openkeyboard-org/OpenDongle/firmware/common/src/rf_task.c

/*
 * UNIFIED RF task body (P6, 2026-06-11 colocation → 2026-07-07 unification):
 * the single 2.4G RF receiver run by ALL THREE chips (CH592, CH582, CH570).
 * Originated as the CH59x (CH592F product) body; the CH570 legacy body
 * (rf_task_ch570.c) converged onto it and was deleted in P6. Chip differences
 * survive only behind the hal seams (hal_timing / hal_rf / hal_dispatch) and
 * the RF_TASK_EXECUTOR_TMOS family switch. Includes resolve per-chip via the
 * building tree's -I src / -I common/include (rf_task.h, CONFIG.h etc.).
 *
 * OpenKeyboard.org OpenDongle
 * Copyright 2026 Eric Molitor (EMulator)
 * SPDX-License-Identifier: Apache-2.0
 * 2.4G RF Receiver Task
 *
 * Reverse-engineered protocol parameters from stock firmware.
 * See PROTOCOL.md for full specification.
 */

#include "dongle_target.h"      /* RF_TASK_EXECUTOR_TMOS + tick constants */
#include "dongle_platform.h"
#if RF_TASK_EXECUTOR_TMOS
#include "CONFIG.h"   /* TMOS: the CH59x-family executor (registration + timers) */
#include "HAL.h"
#endif
#include "dongle_chip.h"   /* per-tree SDK common header; supplies the __risc_v_*
                            * critical-section shim on CH582 (the ch583 SDK's
                            * core_riscv.h predates it -- see ch582 dongle_chip.h) */
#include "rf_task.h"
#include "bond.h"

/* CH570 pair-ACK pre-TX gap (V1, bench-derived 2026-07-10). The real Bridge75
 * needs 1..8 ms between its PAIR_BCAST and our 15-byte pair-ACK; answering
 * immediately misses its receive window and the link flaps forever. The
 * shipping build supplied this ACCIDENTALLY, as the ~6.3 ms busy-wait of
 * PRINT("PAIR_BCAST ..."). Schedule it instead: a delayed post runs the
 * existing RF_EVT_TX_PAIR_15 handler from the pump, so nothing blocks the
 * radio IRQ.
 *
 * Expressed in TMOS units (625 us) like every other delay in this file --
 * hal_event_post_delayed() takes Tsys ticks and CH592 converts back with
 * hal_tmos_units_from_tsys(), so a raw microsecond value would silently
 * quantize there (2000 us -> 3 units -> 1875 us). Stating the unit count makes
 * the quantization explicit and keeps the constant portable if CH59x ever
 * needs the same gap.
 *
 * Sweep: 0 -> 0/3, 500 us -> 2/3, 1000/2000/6337 us -> 3/3, 12 ms -> 1/3,
 * 20 ms -> 0/3. Per-value reconnect quality (bench): 1875 us -> 6/6 but
 * 0.22 s / up to 12 flips; 2500 us -> 8/8, 0.11 s, 0-1 flips (chosen: 4 units).
 * Value set by each target's dongle_target.h. */
#ifndef RF_CH570_PAIR_ACK_PRE_TX_TMOS
#error "RF_CH570_PAIR_ACK_PRE_TX_TMOS must be defined by the target header"
#endif

/* Confirm-before-persist gate (Issue #23): defer the durable bond write until a
 * connected RX confirms the peer accepted the session. Named as its own feature
 * so both executors can share the state machine (the durable-arm site and the
 * CX4 write stay per-executor). Every target header must set it explicitly. */
#ifndef RF_CONFIRM_BEFORE_PERSIST
#error "RF_CONFIRM_BEFORE_PERSIST must be defined by the target header"
#endif

#include "usb_device.h"
#include "hal_timing.h"        /* RF deadline-scheduler seam */
#include "hal_timing_ch592.h"  /* CH592 task-dispatch shim (CONNECTED_POLL slot) */
#include "hal_dispatch.h"      /* deferred-event seam (chip header aliases above) */
#if !RF_TASK_EXECUTOR_TMOS
/* CX1 (codex): CONNECTED-state RF re-arms are timing-critical (the keyboard
 * replies inside the ~875 us window) and the CH570 pump's worst-case latency
 * under EP6 IAP flash traffic is milliseconds — so on this executor the
 * radio-IRQ sink arms them SYNCHRONOUSLY (its validated legacy shape). On
 * TMOS they stay posted events (the validated CH59x shape — CX2). */
static void rf_arm_post_poll_rx(void);
static void rf_rearm_rx(void);
#define RF_CONNECTED_POST_POLL_RX_ARM() rf_arm_post_poll_rx()
#define RF_CONNECTED_RX_REARM()         rf_rearm_rx()
/* CH570 hardware poll grid (ch570/Makefile knob; 0 on other !TMOS ports).
 * When set, the connected-poll cadence is a hardware auto-reload grid
 * anchored at the pair/re-key TX and PROMOTED by ownership transfer
 * (hal_timer_promote_periodic -> st_periodic_transfer, zero hardware
 * writes) instead of re-armed at the promote instant — the CH592 TMR0
 * phase-lock mirror. See analysis/ch570-hw-poll-grid/baseline.md for the
 * +3380 ppm software-grid drift this replaces. */
void hal_timer_promote_periodic(uint8_t from_slot, uint8_t to_slot,
                                uint32_t fallback_period,
                                hal_timer_cb_t cb);  /* hal_timing_ch570.c */
uint8_t hal_timer_grid_nudge(uint32_t ticks);        /* hal_timing_ch570.c */
/* Phase acquisition (Codex option C, 2026-07-08). A crystal-flat grid that
 * starts outside the sleeping keyboard's narrow RX window misses it
 * IDENTICALLY forever (real-Bridge75 finding: promote+bond OK, rx=0 for
 * every poll at two different anchors). The v0.96 software timer acquired
 * by accident: its +3380 ppm drift (~+3 us/poll) swept the phase across the
 * slot until a poll landed and the keyboard's ±31 us/packet servo locked.
 * Deliberate version: start the first period at the promote anchor plus a
 * fixed offset (v0.96's effective mod-slot phase ≈ the ~9.7 ms print delay
 * ≈ +75 us; replace with the measured CH592 value when its probe returns),
 * then, while CONNECTED with zero poll responses, stretch the grid +8 us
 * per poll (Codex band 4-8 us — bigger steps can hop a narrow window) until
 * the first reply, then hold flat.
 * N10 SCOPE (CODEREVIEW, accepted residual): this sweep is LOCAL to one
 * uninterrupted grid — a ~26-poll session covers ~0..267 us, and the step
 * counter does NOT carry physical phase into the next re-anchored session, so
 * full-slot cross-session tiling is NOT achieved. The stock Bridge75 locks in
 * practice (production-validated); a true cumulative-phase primitive is
 * deferred pending a phase-controllable failing control. See rf_ch570_acq_arm
 * and analysis/codex-review-campaign-2026-07-17/change12-N10-sweep-spike.md. */
#define RF_CH570_GRID_PHASE_OFFSET_TICKS 7500u   /* 75 us @100 MHz */
#define RF_CH570_ACQ_STEP_TICKS 800u             /* 8 us per poll */
#define RF_CH570_ACQ_MAX_NUDGES 150u   /* 150*8us=1.2ms; > one full slot only
                                        * at the stock 28-tick interval (875us
                                        * slot) — a larger provisioned interval
                                        * (up to 300 -> 9.375ms slot) is NOT
                                        * covered by this fixed cap (N10) */
static void rf_ch570_acq_arm(uint8_t seed);  /* flash helper below */
static volatile uint32_t rf_ch570_acq_base; /* RX tally at promote:
                                         * ANY connected RX freezes the
                                         * sweep (Codex: the first reply may
                                         * be a LEN-10 HID report, not a
                                         * LEN-1 poll response)             */
static volatile uint32_t rf_ch570_acq_nudges;
/* No TMOS on this executor: map the TMOS mem helpers the body uses onto the
 * builtins. NOTE tmos_memcmp is TRUE-when-EQUAL (BLE-lib convention). */
#define tmos_memcpy(dst, src, n) __builtin_memcpy((void *)(dst), (const void *)(src), (n))
#define tmos_memset(dst, v, n)   __builtin_memset((void *)(dst), (v), (n))
#define tmos_memcmp(a, b, n)     (__builtin_memcmp((const void *)(a), (const void *)(b), (n)) == 0)
/* The sink's internal sta vocabulary — numerically the CH59x BLE-lib codes
 * (CH59xBLE_LIB.h) so telemetry stays comparable across chips. */
#define TX_MODE_TX_FINISH 0x01
#define RX_MODE_RX_DATA   0x03
#define TX_MODE_TX_FAIL   0x11
#else
#define RF_CONNECTED_POST_POLL_RX_ARM() hal_event_post(RF_EVT_POST_POLL_RX)
#define RF_CONNECTED_RX_REARM()         hal_event_post(RF_EVT_RX_RESTART)
#endif
#include "hal_rf.h"             /* RF PHY seam */
#include "rf_protocol.h"        /* shared on-air protocol facts (phase A) */
#include "rf_supervision.h"     /* stock-style supervision timing helpers */

#if !RF_TASK_EXECUTOR_TMOS
/* The acquisition sweep stops as soon as any connected packet is received. */
static volatile uint32_t rf_ch570_connected_rx_count;
#endif
/* RF arm status is recorded in IRQ and task context; task-context guard sites
 * consume it and re-arm when needed. */
volatile uint8_t  rf_last_arm_status;
#if !RF_TASK_EXECUTOR_TMOS
/* Cold-boot SRAM entropy: main() hashes the pristine power-on state of the free
 * RAM gap into this word before normal stack use, and the session-AA RNG mixes
 * it into its seed so each cold boot (i.e. each replug,
 * i.e. each fresh pair in practice) gets a distinct, unpredictable AA rather
 * than the UID-deterministic value. Costs one word — the hashed RAM is the
 * normal stack/heap, not reserved. See ch570_capture_boot_entropy() in main.c. */
volatile uint32_t rf_ch570_boot_entropy;
#endif

/* Supervision/re-acquire runs the production CH592 stock shape — the
 * bench-validated v0.93+ product behavior on every build path (including the
 * CH582 port and direct sub-targets). The legacy OpenDongle-style recovery
 * flavor and its CH592_STOCK_EV10_EXPERIMENT A/B flag were retired in the
 * unify-rf-task P1a collapse (flag had defaulted to 1 since v0.94). */

#define CH592_STOCK_EV10_LAPSE_MARGIN_TICKS 128u
#define CH592_STOCK_EV10_RECOVERY_CONFIRM_WINDOWS 1u
#define RF_RTC_BACKSTEP_TOLERANCE_TICKS 1024u

/* ---------- RF PHY parameters (from firmware RE) ---------- */

/* The product boots directly into the raw 2.4 GHz listener on its configured
 * access address and channel. Pair completion persists the bond to DataFlash
 * so the dongle reconnects after a reboot without reprovisioning. */

/* Promote after this numbered session-AA burst has completed locally.
 * Stock promotes from state 1 on TX_MODE_TX_FINISH; it does not wait for
 * a six-packet recovery burst. The current 08FD/CEBD reconnect bench
 * shows the keyboard reporting CONNECTED after burst #1, so default to
 * the stock-shaped early promote and keep the old "after all bursts"
 * behavior. */
#define RF_BURST_PROMOTE_AFTER_SESSION_BURST 1

#if RF_BURST_PROMOTE_AFTER_SESSION_BURST < 1 || RF_BURST_PROMOTE_AFTER_SESSION_BURST > 6
#error "RF_BURST_PROMOTE_AFTER_SESSION_BURST must be in 1..6"
#endif

/* Tick gap between burst TXes. 1 TMOS tick = 625 µs on CH58x.
 *
 * The keyboard's first-pair branch in FUN_ram_20001192 does two DataFlash
 * persists (FUN_ram_00009a40 writes MAC at flash 0x6000, FUN_ram_00009aa4
 * writes AA at flash 0x4000), each = page-erase (~25ms) + page-write
 * (~5ms). Total RF-callback blocking time: ~50-100 ms before the radio
 * reconfig completes and the library re-arms RX on the new session AA.
 *
 * An immediate-fire burst (tmos_set_event, ~0 ms gap) lands entirely
 * inside that blocked window — verified live: 6 TXes fired in 101 ms,
 * keyboard state stayed 0x35. Pacing each burst TX 80 ticks (~50 ms)
 * apart puts burst#2 at +50ms, burst#3 at +100ms, etc. — burst#3..5 are
 * past the DataFlash blocking window and should land on a re-armed
 * keyboard RX.
 *
 */
#define RF_PAIR_ACK_BURST_GAP 80

/* Pair-completion defaults. Keep these before static initializers that
 * reference them.
 *
 * RF_SESSION_ACCESS_ADDR: session AA we'll advertise in the pair-completion.
 * Must match one of the dongle's generator patterns. 0x6A7DAEE6 was dumped
 * live from the stock dongle's SRAM so we know it passes validation.
 *
 * RF_DONGLE_MAC_*: MAC we'll advertise as the "dongle" in the 15-byte
 * pair-completion frame. Two valid choices depending on the test target:
 *   (a) Bench test against a fresh CH592F dev board running stock keyboard
 *       fw (no stored peer): use this chip's own factory BLE MAC so the
 *       bond is durable across reboots. Default below.
 *   (b) Field test against a real Bridge75 keyboard already bonded to its
 *       stock dongle: use the stock dongle's MAC 0xBA 0x47 0x8B 0x72 0xAB
 *       0x3C (read live from its SRAM at 0x20003849..0x2000384E) so the
 *       keyboard matches us on the known-peer branch without touching its
 *       pairing memory.
 * The advertised dongle MAC is held at runtime in rf_bond_dongle_mac,
 * defaulting to RF_DONGLE_MAC_* and overridden from the DataFlash bond
 * record. */
#define RF_SESSION_ACCESS_ADDR   0x6A7DAEE6u
#define RF_DONGLE_MAC_0 0xD1
#define RF_DONGLE_MAC_1 0x4C
#define RF_DONGLE_MAC_2 0x85
#define RF_DONGLE_MAC_3 0x26
#define RF_DONGLE_MAC_4 0x3B
#define RF_DONGLE_MAC_5 0x38

/* 15-byte pair-ACK payload. The session access address and dongle MAC must
 * match the advertised session identity for reconnect tests; otherwise the
 * keyboard can receive a completion packet but enter connected mode on the
 * wrong AA / peer identity. */
/* RF_PAIR_TIMEOUT — advertised conn_timeout in our 15-byte pair-ACK.
 * Default 600 matches what the keyboard's pair broadcast advertises. */
#define RF_PAIR_TIMEOUT RF_PROTO_DEFAULT_TIMEOUT
#define RF_PAIR_ACK15_ACCESS_ADDR RF_SESSION_ACCESS_ADDR

static uint8_t rf_pair_ack15[15] = {
    /* session access addr (MSB-first u32) */
    (uint8_t)((RF_PAIR_ACK15_ACCESS_ADDR >> 24) & 0xFF),
    (uint8_t)((RF_PAIR_ACK15_ACCESS_ADDR >> 16) & 0xFF),
    (uint8_t)((RF_PAIR_ACK15_ACCESS_ADDR >>  8) & 0xFF),
    (uint8_t)( RF_PAIR_ACK15_ACCESS_ADDR        & 0xFF),
    /* type tag (also seeds the data-hop index on both ends via % 5) */
    RF_PROTO_PAIR_ACK_TYPE,
    /* conn_interval (u16 LE) = 0x001C = 28. MUST match the keyboard's
     * advertised conn_interval in PAIR_BCAST. The keyboard hops data
     * channels every conn_interval protocol ticks of 1/32000 s
     * (= 875 µs at 28 — the "32K" clock is the calibrated 32000 Hz
     * LSI, not 32768 Hz); our TMR0 POLL cadence derives from this same
     * value via rf_tmr0_steady_count(). Advertising 0x001E = 30 (the
     * previous value) caused a ~10% rate mismatch: fw-ch592f polls at
     * 937 µs while the keyboard hops at 875 µs, so polls land outside the
     * keyboard's RX window after a few hops and the link drops at
     * ~3 s. Found 2026-05-20 via keyboard SRAM dump (rx_count=0
     * post-CONNECTED). See
     * analysis/fw-ch592f-vs-stock-audit-2026-05-20.md G3. */
    (uint8_t)(RF_PROTO_DEFAULT_INTERVAL & 0xFF),
    (uint8_t)((RF_PROTO_DEFAULT_INTERVAL >> 8) & 0xFF),
    /* conn_timeout (u16 LE) — RF_PAIR_TIMEOUT bytes LE */
    (uint8_t)(RF_PAIR_TIMEOUT & 0xFF),
    (uint8_t)((RF_PAIR_TIMEOUT >> 8) & 0xFF),
    /* our (dongle) MAC */
    RF_DONGLE_MAC_0, RF_DONGLE_MAC_1, RF_DONGLE_MAC_2,
    RF_DONGLE_MAC_3, RF_DONGLE_MAC_4, RF_DONGLE_MAC_5,
};

/* Burst state machine — accessed from both IRQ (TX_FINISH callback) and
 * task context (RF_EVT_TX_PAIR_15B handler). volatile for IRQ safety. */
volatile uint8_t rf_inject_burst_active = 0;
volatile uint8_t rf_inject_burst_idx = 0;  /* 0..5, 0 = first TX in flight */

/* Channel set for the burst. The keyboard's first-pair radio reconfig
 * (FUN_ram_000072e6 in firmwareB.bin) does only RF_Shut + RF_Config —
 * it sets the session AA but does NOT change channel. So immediately
 * after first-pair the keyboard is listening on session AA on whichever
 * pair channel it last broadcast on (∈ {8, 17, 26}). Hitting the data
 * LUT {4, 13, 20, 28, 33} therefore misses the keyboard entirely in
 * state==1. Burst on the pair LUT instead.
 *
 * Two rounds of the shared pair LUT (rf_pair_channels, declared below from
 * RF_PROTO_PAIR_CHANNELS_INIT) give 6 chances spaced over the burst window —
 * biases for the keyboard's listen channel being one of those three. The
 * burst indexes the LUT modulo its size (rf_burst_channel(idx)) so a
 * pair-channel change in rf_protocol.h propagates here automatically. */
#define RF_BURST_TX_COUNT (2u * RF_PROTO_PAIR_CHANNEL_COUNT)

volatile uint8_t rf_supervision_ev10_active = 0;

/* LED-relay queue counter — increments each time rf_queue_led_relay() queues a
 * host LED byte for the poll path. SWD oracle to confirm the relay was queued
 * (the on-air TX is then confirmed by the keyboard's 5A status). */

/* 1760u diag: count faithful-EV10 attempts that completed (caught
 * the LEN-10, sent the LEN-15 re-key, returned to CONNECTED) vs aborted (no
 * LEN-10 in the budget). */

/* Hop-clock timestamp (rf_hop_read(): HSE-derived protocol ticks) captured at
 * the EV10 LEN-15 re-key RF_Tx. Used by RF_EV10_GRID_ALIGNED_POLL to phase
 * the first resumed data poll to rekey_TX + 1 interval (stock's measured
 * convention), independent of the post-TX reconfigure latency. */
volatile uint32_t rf_ev10_rekey_tx_hop;

/* Stock-shaped queued app payload. Per disasm of stock firmware.bin,
 * event 0x80 (LED relay) doesn't transmit directly — it queues
 * [0xA1, LED_byte] and the normal event 0x02 (poll) helper prepends
 * the control byte and sends as [ctrl][0xA1][LED_byte] in the next
 * poll slot. Same TMR0 cadence, same hop schedule — the keyboard's
 * CONNECTED-state RX only listens in those slots, so out-of-band
 * direct LED TX lands in dead air.
 *
 * rf_app_tx_pending nonzero ⇒ rf_send_poll consumes the queue
 * (sends 3-byte [ctrl,buf[0],buf[1]] instead of 1-byte [ctrl]) while
 * decrementing the count. Stock parity: a single LEN=3 relay per host LED
 * change + one at connect/reconnect -- no burst, no periodic heartbeat. */
volatile uint8_t  rf_app_tx_pending;
volatile uint8_t  rf_app_tx_buf[2];

/* Queue the host->keyboard LED relay payload [0xA1][led] so the next connected
 * poll sends it as [ctrl][0xA1][led] (rf_send_poll consumes rf_app_tx_pending).
 * Replaces the stock-shaped delayed RF_EVT_POST_PROMOTE_LED3 event, which the
 * supervision/EV10 rebind paths cancelled before it could fire (the relay never
 * transmitted). The queue buffer is NOT cancelled by those rebind stop sites, so
 * it survives to the next valid poll. Caller contexts are NOT both cooperative:
 * RF_SetLEDState runs in TMOS task context, but the burst-promote re-sync runs
 * inside rf_phy_event_sink -- an IRQ-tail deferred callback that CAN preempt
 * task context (see the P2.4 note at the sink). No IRQ critical section is
 * needed anyway because every shared item (rf_led_state, rf_app_tx_buf bytes,
 * rf_app_tx_pending) is a single volatile byte (atomic on RV32), preemption is
 * strictly one-way (sink over task, never the reverse), and the foreground
 * latches rf_led_state BEFORE any queue access -- so every interleaving
 * converges to the queue holding the current LED byte with pending=1. */
static __attribute__((noinline)) void rf_queue_led_relay(uint8_t led)
{
    rf_app_tx_buf[0]  = RF_PROTO_HID_TAG;
    rf_app_tx_buf[1]  = (uint8_t)(led & 0x07u);
    rf_app_tx_pending = 1u;          /* stock parity: single LEN=3 relay, fire-and-forget */
}

/* Stock dispatcher event 0x04 calls RF_Rx(gp-0x604, 10, 0xff, 0xff):
 * the same control/poll buffer used by empty-poll RF_Tx, but with RX
 * length 10. The shared poll/RX buffer itself is the normal rf_poll_buf below. */

/* Product reconnect default. */
#define RF_DEFAULT_ACCESS_ADDR  0xAC1649CEu


/* CRC initial value */
/* CRC init + LLE mode moved to hal_rf_ch592.c (P2.4) -- the PHY seam owns
 * the rfConfig_t construction. */

/* LLE mode: 2M PHY | basic mode | whitening ON | channel index | RSSI byte */
/* Stock dongle's rfConfig.LLEMode = 0x10 (BASIC + WHITENING_ON +
 * PHY_2M) per the OQ7 SRAM dump. Keyboard uses 2M PHY. Bench-proven
 * 2026-05-17: with PFIC_EnableIRQ(BLEB|BLEL) + RF_Rx(NULL,0,...) +
 * LLEMode=0, fw-ch592f receives 241 RX_DATA callbacks/10s on BLE
 * ADV ch37 (1M PHY). Restoring LLEMode=0x10 for 2M PHY compatibility
 * with the keyboard's proprietary 2.4G protocol. */

/* Minimum RSSI for pair acceptance (dBm). Gates the fresh-pair path (no
 * valid bond) AND a boot-window accept of a DIFFERENT keyboard; the
 * known-peer reconnect path has no RSSI gate (a bonded keyboard must
 * reconnect at range).
 *
 * This floor has now been raised twice for the same reason, which is the
 * point worth carrying forward: -55 rejected most real captures, and -75
 * rejected the product's primary scenario. Bisected with diagnostic builds
 * on stock v0.96.15 with a bonded link: -128 accepted, -90 accepted, -82
 * accepted, -75 REJECTED. So the keyboard's pair broadcast arrives at
 * -81..-76 dBm with both boards on one bench - i.e. -75 had NEGATIVE margin
 * at legitimate pairing distance, and a dongle behind a PC case or across a
 * desk sits in that band or below.
 *
 * -90 keeps what the gate is actually for. Its job is stopping an
 * unprovisioned dongle auto-pairing with a distant keyboard in a dense
 * environment; at 2.4 GHz a cross-room signal (several metres plus a wall)
 * generally lands below -90 while same-room stays above it. That preserves
 * the "not the neighbour's office" property with ~10 dB over what we
 * measured, instead of defending a threshold the bench already fails.
 *
 * Treat this as a heuristic sanity floor, not a security boundary. CH59x
 * RSSI is coarse and uncalibrated chip to chip, so the same number means
 * different real distances on different units, and the gate is reported
 * inert on the CH570 SKU (its RSSI byte reads constant) - so the product
 * line already tolerates a no-gate configuration.
 *
 * If mispairing in dense environments ever becomes a real complaint, the
 * fix is NOT a tighter floor: it is strongest-candidate selection - collect
 * broadcasters briefly during pairing and take the highest RSSI, keeping
 * this only as a sanity floor. An absolute threshold encodes antenna and
 * geometry assumptions; relative selection targets the actual failure mode.
 *
 * Overridable for bench profiles without editing source (this file is shared,
 * so substitute the chip you are building):
 *   make -C firmware ch570 PAIR_MIN_RSSI=-95
 *   make -C firmware ch592 PAIR_MIN_RSSI=-95
 * The live value is readable over IAP (status byte
 * DONGLE_STATUS_OFF_LAST_RSSI), so re-measuring at a different geometry
 * does not need four diagnostic builds the way this bisect did. */
#ifndef RF_PAIR_MIN_RSSI
#define RF_PAIR_MIN_RSSI        (-90)
#endif

/* Pairing packet payload length (exactly 10 bytes) */
#define RF_PAIR_PKT_LEN         RF_PROTO_LEN_PAIR_BCAST

/* Connection timeout in TMOS ticks (1600 = 1 second). Default 5 seconds. */
#define RF_CONN_TIMEOUT_TICKS   (1600 * 5)

/* 15-byte pair-completion TX buffer. Populated at pair-accept time
 * from the layout we reversed via the sniffer's PAIR_ACK decoder and
 * the stock firmware's RF_Tx call at VA 0x8c38:
 *   [0..3]  session access address (MSB-first u32)
 *   [4]     type tag (<5)
 *   [5..6]  conn_interval (u16 LE)
 *   [7..8]  conn_timeout  (u16 LE)
 *   [9..14] dongle MAC (6 bytes)
 * Keyboard validator: type<5 + AA matches 0x6A????E6 or 0xAC????CE.
 * TX channel is whichever channel the broadcast RX left the radio on —
 * matching stock event 0x40, which doesn't call RF_SetChannel. */
static uint8_t rf_pair_ack_buf[15] = {0};

/* RF_SESSION_ACCESS_ADDR / RF_DONGLE_MAC_* are defined (with full rationale)
 * in the single defaults block near the top of the file. */

#define RF_POLL_TX_LEN          RF_PROTO_LEN_POLL
#define RF_POST_POLL_RX_LEN    10u

/* CONNECTED-mode poll state. LEN=1 poll payload is a single control
 * byte; the stock dongle emits `ctrl ∈ {0x00, 0x03}` on the session AA
 * every 28 RTC32K ticks (~875 us, ~1143/s total), rotating across the
 * 5-channel data LUT. Stock parity builds should use the RTC-derived
 * formula rather than the older phase-arbitrary sequence rotation.
 *
 * Stock uses the same gp-0x604 pointer for empty-poll RF_Tx length 1
 * and post-poll RF_Rx length 10. Size this buffer for the RX arm while
 * keeping the TX length explicit at RF_POLL_TX_LEN. */
static uint8_t rf_poll_buf[RF_POST_POLL_RX_LEN] = { 0x00 };
static const uint8_t rf_data_channels[RF_PROTO_DATA_CHANNEL_COUNT] =
    RF_PROTO_DATA_CHANNELS_INIT;
static uint8_t rf_data_ch_idx;

/* Stock event 0x20 uses the pair-channel LUT {8,17,26} and calls
 * RF_Rx(gp-0x604, 6, ...). The exact on-air effect of that RF_Rx(6)
 * pre-phase is still unresolved, but it clearly exists in stock and
 * is separate from event 0x40's explicit 15-byte RF_Tx. */
static const uint8_t rf_pair_channels[RF_PROTO_PAIR_CHANNEL_COUNT] =
    RF_PROTO_PAIR_CHANNELS_INIT;
static uint8_t rf_pair_prep_idx;
static uint8_t rf_pair_prep_buf[6] = { 0 };
/* Stock connection_setup stores 0x30 into gp-0x614 and event 0x20
 * reschedules itself on that interval while state==1. TMOS ticks are
 * 625 us here, so 0x30 ticks = 30 ms. */
#define RF_PAIR_PREP_TICKS      0x30
/* CONNECTED-state RX counters — written from the RF IRQ, read from
 * task context. Purpose: tell us whether any session-AA traffic is
 * getting through while we experiment with poll rates / hop strategy.
 * Volatile so the compiler doesn't hoist reads across the IRQ/task
 * boundary. */



/* ---------- TMR0-driven poll / EV10 re-key pacing ----------
 *
 * Stock dongle times its 2.4 GHz event cadence off TMR0, not off TMOS
 * (PROTOCOL.md §"Timer-driven event scheduling"). TMR0 counts at the
 * current system clock (Tsys = 60 MHz via SetSysClock(CLK_SOURCE_PLL_60MHz)
 * in main.c; no prescaler). On CYC_END the TMR0 IRQ posts the next RF
 * task event, giving us microsecond-precision pacing independent of
 * the TMOS 625 µs scheduling tick.
 *
 * Two counts are relevant:
 *   - First pair-completion delay: 0x4650 = 18000 Tsys counts = 300 µs.
 *     Armed in the PAIRING RX callback on pair-accept, before the first
 *     15-byte TX fires.
 *   - Steady-state poll / pair-completion: conn_interval * 1875 Tsys
 *     counts. With the stock keyboard's conn_interval=28 this is 52500
 *     counts = 875 µs → ~1142.9 Hz, which matches the observed live
 *     poll rate of the stock dongle.
 *
 * TMR0 is periodic (CYC_END reloads and keeps counting). The IRQ
 * handler dispatches on rf_state, so the same free-running timer drives
 * the EV10 pair-ACK pacing and CONNECTED polling without
 * re-arming per transition. Event-handler helpers re-init TMR0 only
 * when the period itself changes — notably on the first pair-completion
 * TX, where the 300 µs bootstrap gets replaced with the steady-state
 * conn_interval-derived count. */
#define RF_TMR0_PAIR_INIT_COUNT   (300u * HAL_TICKS_PER_US)   /* 300 µs in Tsys (18000 @ 60 MHz) */
#define RF_TMR0_DEFAULT_INTERVAL  RF_PROTO_DEFAULT_INTERVAL           /* stock keyboard's conn_interval — fallback before a pair broadcast sets rf_conn_interval */

/* rf_tmr0_start/stop are non-static: the hal_timing_ch592 seam drives them for
 * the CONNECTED_POLL slot (declared in hal_timing_ch592.h). */
static uint32_t rf_tmr0_steady_count(void);
static uint32_t rf_connected_poll_delay_count(uint32_t delay_ticks);

/* ---------- State ---------- */

#if RF_TASK_EXECUTOR_TMOS
static uint8_t rf_taskID;   /* TMOS task handle (the dispatch macros use it) */
#endif
/* volatile: rf_state is written from task/IRQ-tail-callback context and READ in
 * the true TMR0 hardware ISR (rf_tmr0_isr_dispatch posts the event matching the
 * current rf_state), so it must not be cached across that read. */
static volatile uint8_t rf_state;
/* Latest host HID LED byte (CapsLock/NumLock/ScrollLock, low 3 bits). Set by
 * RF_SetLEDState from the foreground; queued directly via rf_queue_led_relay
 * (sent as [ctrl][0xA1][led] by the next poll). Persists across reconnect so
 * the post-promote re-sync restores the keyboard LED. */
static volatile uint8_t rf_led_state;
static int8_t  rf_rssi;
#if DONGLE_BENCH_DROP_FIRST_HID
static volatile uint8_t  rf_bench_drop_armed;   /* set at promote; the next non-zero HID is swallowed */
static volatile uint16_t rf_bench_drops;        /* SWD-readable: injected drops so far */
#endif

/* Pairing data */
static uint32_t rf_access_addr;
static uint8_t  rf_channel;
static uint8_t  rf_peer_mac[6];
static uint16_t rf_conn_interval;
static uint16_t rf_conn_timeout;

/* Pre-reboot quiesce latch (RF_QuiesceRequest / RF_Quiesced). volatile: set
 * in executor context, polled by the main loop, read by the IRQ-context
 * gates in the timing callbacks and the PHY sink. One-way until reset. */
static volatile uint8_t rf_quiesced;

/* ---------- IAP 0x92 RF diagnostics ----------
 * Wrapping u32 counters and a few "last" bytes, incremented in place (task or
 * IRQ-tail context, no locking: a lost increment is acceptable for a
 * diagnostic). Read-only over USB via RF_DiagFill(); nothing here feeds back
 * into the protocol. Increments sit AFTER the radio arm on hot paths. */
static volatile uint32_t rfd_len10_seen;             /* LEN-10 reaching the not-connected accept gate */
static volatile uint32_t rfd_len10_accept_known;     /* accepted as a known-durable reconnect */
static volatile uint32_t rfd_len10_accept_fresh;     /* accepted as a fresh/tentative pair */
static volatile uint32_t rfd_len10_rejected;         /* fell through the accept gate */
static volatile uint32_t rfd_len10_ev10_seen;        /* LEN-10 seen by the EV10 reacquire branch */
static volatile uint32_t rfd_pair_ack_posted;        /* RF_EVT_TX_PAIR_15 scheduled */
static volatile uint32_t rfd_pair_ack_tx_ok;         /* pair-ACK StartTx rc == 0 (first + burst) */
static volatile uint32_t rfd_pair_ack_tx_fail;       /* pair-ACK StartTx rc != 0 */
static volatile uint32_t rfd_pair_ack_tx_done;       /* TX_FINISH while the burst was active */
#if DONGLE_DELIVERY_COUNTERS
static volatile uint16_t rfd_hid_rx;                 /* HID reports (peer-matched 0xA1) received over RF in CONNECTED, pre-forward/pre-dedup */
static volatile uint16_t rfd_hid_rx_down;            /* of those, non-zero (key-down) payloads: compare to controller ll_hid_tx_done_down => RF loss */
#endif
static volatile uint32_t rfd_rx_restart_handled;     /* RF_EVT_RX_RESTART re-arm attempts (a failed
                                                      * arm counts too; it schedules the P4 retry) */
static volatile uint32_t rfd_rx_restart_dropped_ev10;/* RF_EVT_RX_RESTART dropped (EV10 scan owns RX) */
static volatile uint32_t rfd_arm_retry_scheduled;    /* P4 guard: retry posted after a failed arm */
static volatile uint32_t rfd_supervision_lapses;     /* connected supervision lapsed */
static volatile uint32_t rfd_ev10_entries;           /* EV10 reacquire scans started */
static volatile uint32_t rfd_ev10_giveups;           /* EV10 watchdog expired -> reconnect camp */
static volatile uint32_t rfd_pair_prep_runs;         /* EV10/pairing pair-prep RX arms */
static volatile uint32_t rfd_ev10_ack_tx;            /* EV10 re-key ACK StartTx attempts */
static volatile uint32_t rfd_ev10_ack_tx_fail;       /* ... that returned non-zero */
static volatile uint32_t rfd_connected_promotes;     /* rf_state -> CONNECTED */
static volatile uint32_t rfd_fresh_relistens;        /* rf_return_to_fresh_pair */
static volatile uint32_t rfd_bootwin_closes;         /* boot window closed -> reconnect camp */
static volatile uint32_t rfd_confirm_armed;          /* fresh promote entered WAIT_RX */
static volatile uint32_t rfd_confirm_to_waitrx;      /* confirm deadline fired unconfirmed */
static volatile uint32_t rfd_confirm_to_waitrearm;   /* confirm deadline fired confirmed */
static volatile uint32_t rfd_persist_attempts;       /* bond_save calls */
static volatile uint32_t rfd_persist_ok;             /* readback matched */
static volatile uint32_t rfd_pump_passes;            /* RF_TaskPump calls (CH570) */
static volatile uint32_t rfd_ack_accept_systick;     /* SysTick at the LEN-10 accept (sink) */
static volatile uint32_t rfd_ack_tx_systick;         /* SysTick at the first pair-ACK StartTx */
static volatile uint32_t rfd_ack_latency;            /* accept -> StartTx, SysTick ticks */
static volatile uint32_t rfd_ack_tx_duration;        /* StartTx -> TX_FINISH of the first ACK */
static volatile uint32_t rfd_last_ack_aa;            /* access address the last pair-ACK went out on */
static volatile uint32_t rfd_reacq_entry_systick;    /* hal_timing_systick_now() at reacquire entry */
static volatile uint32_t rfd_giveup_systick;         /* ... at the give-up camp */
static volatile uint8_t  rfd_len10_last_disp;        /* RFD_L10_* of the last LEN-10 */
static volatile uint8_t  rfd_persist_last_reason;    /* RFD_PERSIST_* of the last persist task run */
static volatile uint8_t  rfd_last_save_rc = 0xFFu;   /* last bond_save rc (0xFF: none) */
static volatile uint8_t  rfd_last_pair_ack_tx_rc = 0xFFu; /* last pair-ACK StartTx rc (0xFF: none) */
enum {
    RFD_L10_NONE = 0, RFD_L10_ACCEPT_KNOWN = 1, RFD_L10_ACCEPT_FRESH = 2,
    RFD_L10_REJ_TOMBSTONE = 3, RFD_L10_REJ_LOCKED = 4, RFD_L10_REJ_BAD_MAC = 5,   /* zero, all-FF or own MAC */
    RFD_L10_REJ_RSSI = 6, RFD_L10_REJ_OTHER = 7, RFD_L10_EV10 = 8
};
enum {
    RFD_PERSIST_NONE = 0, RFD_PERSIST_SEMANTIC = 1, RFD_PERSIST_SAVE_FAIL = 2,
    RFD_PERSIST_READBACK = 3, RFD_PERSIST_TOMBSTONE = 4, RFD_PERSIST_ALREADY = 5,
    RFD_PERSIST_OK = 6
};


/* Runtime bond identity. These default to the compiled-in identity, so an
 * un-provisioned chip behaves exactly as before; RF_TaskInit() overrides them
 * from a DataFlash bond record when one is present (see rf_load_persistent_bond
 * and bond.c). Every runtime use of the session/default access address reads
 * these instead of the macros, which makes the binary identity-agnostic rather
 * than pinned to one keyboard. The static rf_pair_ack15[] initializer and the
 * speculative-path buffer builds still reference the macros (compile-time
 * defaults / not in the shipping build); rf_pair_ack15[] is patched at init. */
static uint32_t rf_bond_aa         = RF_SESSION_ACCESS_ADDR;
static uint32_t rf_bond_default_aa = RF_DEFAULT_ACCESS_ADDR;

/* ----- Stock-style boot reconnect/pair window (Step 5) -----
 * With a valid (non-zero-AA) bond present, the dongle spends ~3 s after boot
 * alternating its listen AA between the bond's session AA (reconnect, the
 * tick-0 default so it is always tried first) and the pair AA (so a new
 * keyboard can still pair during the window, e.g. after a replug), then
 * settles on reconnect-only. Mirrors the stock dongle's event-0x200 boot
 * behavior. A fresh/un-provisioned dongle (no valid bond) leaves rf_bond_valid
 * at 0, skips the window, and stays in pairing forever (its existing path). */
/* RF_BOND_FROM_DATAFLASH gates both the boot window (below, used from ~line 2178
 * and in RF_ProcessEvent) and the bond loader (~line 4276). Its default is also
 * declared next to the loader, but that is ~1000 lines AFTER the boot-window
 * #if blocks — so it MUST be defaulted here, before first use, or the window
 * silently compiles out (the macro reads as 0/undefined at those earlier #ifs).
 * The later #ifndef then no-ops. */
#define RF_PAIR_ACCESS_ADDR RF_PROTO_PAIR_ACCESS_ADDR
#define RF_BOOT_WINDOW_STEPS 10u   /* 10 x 300 ms ~= 3 s, like stock 0x200 */
#define RF_BOOT_WINDOW_TICKS 480u  /* 300 ms in 625 us TMOS units (0x1e0) */

/* P3a: hal_timing deltas are Tsys ticks (hal_timing.h contract); the CH592
 * shim divides back to the 625 us TMOS units its backing timers want. This
 * is the TMOS-unit deadline expressed in Tsys -- an exact multiple, so the
 * armed TMOS value is bit-identical to the pre-P3a literal. */
#define RF_BOOT_WINDOW_TICKS_TSYS      (RF_BOOT_WINDOW_TICKS * HAL_TMOS_UNIT_TICKS)

/* Terminal-camp liveness watchdog. Every terminal camp (EV10 give-up, closed
 * boot window, unbonded start) arms RX once and then leans on the radio's
 * own events to re-drive it: a lost completion, or a PHY that went deaf,
 * left the dongle in "waiting for reconnect" until a chip reset, because
 * the arm-status guard (rf_arm_retry_if_failed) never fires on either radio
 * library (TODO: "no time-based liveness backstop"; one such strand seen on
 * the bench 2026-09-04). The camp now keeps the boot-window slot, free in
 * every terminal camp, as a 200 ms tick. A tick that saw an RX-side event
 * since the last one (data, CRC error or timeout, from the PHY counters)
 * leaves the radio alone. A silent tick re-arms RX from task context under
 * the same IRQ mask as the 0x94 ladder: on CH59x basic-mode RX has no
 * timeout, so a silent camp is the normal state and every silent tick
 * re-arms preventively (shut + config + RX, ~100 us of a 200 ms period);
 * on CH570 the 30 ms camp timeout keeps the counter moving, so a silent
 * tick means the loop died, and the second in a row escalates to shut +
 * vendor re-init + re-arm (rung 2 of the 0x94 ladder, the same code path,
 * instrumented on CH570 but not bench-verified here; a second RF_RoleInit is
 * not validated on the TMOS radio and is not attempted).
 * The tick self-disables outside the exact terminal camp, and the burst
 * accept in the radio sink cancels the slot along with the boot window.
 * Bounds: a lost completion is re-armed within two ticks (the tick after
 * the loss may still read the event that preceded it); rung 3 resets the
 * baseline, so it is re-armed at the next tick. Not covered: a CH570 PHY
 * that keeps raising its 30 ms timeouts while receiving nothing looks alive
 * to this test, which measures event-loop progress, not reception (TODO). */
#define RF_CAMP_WD_TICKS_TSYS          (320u * HAL_TMOS_UNIT_TICKS)   /* 200 ms */
_Static_assert(RF_CAMP_WD_TICKS_TSYS < (1u << 26), "CH570 one-shot arms are 26-bit");
static volatile uint8_t rf_camp_wd_active; /* the boot-window slot is the camp tick; the radio sink clears it */
static uint8_t  rf_camp_wd_silent;        /* consecutive silent ticks (saturating) */
static uint32_t rf_camp_wd_seen;          /* PHY RX-side event count at the last tick */
static volatile uint16_t rfd_camp_wd_rearms;    /* page 1 [60..61], u16 (the page is otherwise full) */
static volatile uint16_t rfd_camp_wd_reinits;   /* CH570 rung-2 escalations; no page byte left: debugger only */
static uint8_t rf_bond_valid;          /* a valid, non-zero-AA bond loaded     */
/* Deferred bond-persist state (see rf_request_bond_persist / rf_persist_bond_task).
 * Declared here (ahead of RF_ProcessEvent) since the RF_EVT_PERSIST_BOND handler
 * touches rf_bond_persist_pending. */
static volatile uint8_t rf_bond_persisted; /* rf_bond_persisted == the RAM tuple matches a
                                            * VERIFIED DataFlash record (set on TMOS load /
                                            * idempotent-match / verified save; cleared when
                                            * a fresh candidate overwrites the tuple). */
static volatile uint8_t rf_bond_persist_pending; /* event posted, write not yet done */
static bond_record_t rf_bond_pending_rec __attribute__((aligned(4))); /* snapshot   */
/* CODEREVIEW N08: the chip's factory MAC, captured at RF_TaskInit BEFORE any
 * record override rewrites rf_bond_dongle_mac. Feeds the semantic validator's
 * own-identity leg (boot load + IAP BondWrite via RF_FactoryMac()). */
static uint8_t rf_factory_mac[6];
/* CODEREVIEW N09: set when the loaded record carried a nonzero dongle_mac
 * override. Auto-persist then carries the ACTIVE advertised identity into the
 * new record instead of silently reverting it to zero (= chip-derived) — the
 * keyboard bonded to the OVERRIDE MAC, so a zero-persisted record broke the
 * next boot's supervision re-key identity. Per-boot (reset re-derives it from
 * the record); a fresh chip / plain pair keeps the zero = chip-MAC semantics. */
static uint8_t rf_dongle_mac_overridden;
/* CODEREVIEW N06: set by RF_TombstoneBond() when the host clears the DataFlash bond
 * over IAP (BondClear). It invalidates the in-RAM bond and BLOCKS any deferred
 * persist from re-writing it AND blocks accepting/promoting a new pair, until the
 * next MCU reset (power-on/reset zeroes .bss -- deliberately NOT lifted at
 * RF_EVT_START, so a delayed-RF-init BondClear on CH570 stays a completed clear).
 * Without it the running RF task's still-valid in-RAM bond (or an already-posted
 * RF_EVT_PERSIST_BOND) re-saves the record the host just erased -- so the clear
 * does not survive to the next boot (bench-observed CH570). */
static volatile uint8_t rf_bond_tombstone;

#if RF_CONFIRM_BEFORE_PERSIST
/* CODEREVIEW N11 (Issue #23: shared by both executors): defer the durable
 * fresh-pair bond write until a connected RX confirms the peer accepted the
 * session. rf_confirm_state runs NONE -> WAIT_RX (fresh promote, awaiting
 * confirm, deadline armed) -> WAIT_REARM (confirm RX seen, awaiting a SUCCESSFUL
 * RX re-arm before the flash write). rf_pair_is_fresh is captured at the
 * pair-broadcast accept: a promote is tentative unless it is a KNOWN DURABLE
 * reconnect (bond valid AND already persisted AND on the bond session AA AND
 * same peer MAC). Ported to CH570 (Issue #23) so a fresh pair that promoted on
 * our own pair-ACK TX-finish alone never persists a dead bond. */
#define RF_CONFIRM_STATE_NONE       0u
#define RF_CONFIRM_STATE_WAIT_RX    1u
#define RF_CONFIRM_STATE_WAIT_REARM 2u
/* 1200 x 625 us = 0.75 s. "TMOS" here names the 625 us tick unit
 * (HAL_TMOS_UNIT_TICKS, defined on both chips), not the executor. */
#define RF_CONFIRM_TIMEOUT_TMOS 1200u
static volatile uint8_t rf_confirm_state;
static uint8_t rf_pair_is_fresh;
#endif /* RF_CONFIRM_BEFORE_PERSIST */
#if RF_TASK_EXECUTOR_TMOS
/* Codex full-batch review (merge blocker): set by a burst-active async TX_FAIL in
 * the radio callback (IRQ) to defer the dual-AA fresh-pair fallback to task
 * context — rf_return_to_fresh_pair does RF_Shut+reconfigure, illegal from the
 * callback. Without it a burst TX_FAIL re-arms RX on the session AA only and can
 * strand a keyboard that missed the first pair-AA ACK on the pair AA. */
static volatile uint8_t rf_burst_txfail_fallback;
#endif
static uint8_t rf_boot_window_active;  /* the alternating window timer is live  */
static uint8_t rf_boot_window_step;    /* tick counter 0..RF_BOOT_WINDOW_STEPS  */
static uint8_t rf_pair_window_open;    /* new-keyboard pairing currently allowed*/
static uint8_t rf_stock_first_supervision_armed;

/* Dongle MAC advertised in the supervision re-key. The keyboard matches this
 * against its stored dongle MAC to accept the LEN-15 re-key, so it must track
 * the bond (not the compiled default) or supervision fails for a dongle whose
 * bond differs from the compiled identity. Defaults to the compiled MAC. */
static uint8_t  rf_bond_dongle_mac[6] = {
    RF_DONGLE_MAC_0, RF_DONGLE_MAC_1, RF_DONGLE_MAC_2,
    RF_DONGLE_MAC_3, RF_DONGLE_MAC_4, RF_DONGLE_MAC_5
};

/* HID data callback */
static rf_hid_cb_t rf_hid_callback;

/* CH59x-BLE-lib RF-descriptor arena poke: the stock CH592 firmware writes the
 * next TX channel + a late byte into the BLE library's internal RF config
 * cells at a FIXED SRAM address before each connected-poll RF_Tx. This is
 * LIBCH59xBLE-specific and the address lives in CH592's 26 KB SRAM. On the
 * CH570 (RFIP radio, 12 KB SRAM) it is both meaningless — the channel is set
 * via hal_rf_set_channel/the RFIP descriptor — and FATAL: 0x200060A0 is far
 * past the CH570 SRAM top (load access fault, P4-caught). No-op off TMOS. */
#if RF_TASK_EXECUTOR_TMOS
#define RF_STOCK_RF_ARENA_BASE ((volatile uint32_t *)0x200060A0u)

static void rf_stock_stage_channel_arena(uint8_t channel, uint8_t late_byte)
{
    uint32_t a0 = RF_STOCK_RF_ARENA_BASE[0];

    RF_STOCK_RF_ARENA_BASE[0] =
        (a0 & 0xFFFF0000u) | ((uint32_t)channel << 8) | 0x10u;
    RF_STOCK_RF_ARENA_BASE[11] = ((uint32_t)late_byte << 24);
}

static void rf_stock_stage_poll_arena(void)
{
    uint8_t late_byte =
        (uint8_t)rf_conn_interval;
    rf_stock_stage_channel_arena(rf_channel, late_byte);
}
#else
static inline void rf_stock_stage_poll_arena(void) { }
#endif

#if RF_TASK_EXECUTOR_TMOS
/* CH59x-family only: the RTC32K counter register (diag validator + entropy).
 * Since P3a nothing on the product path measures time with it. */
#define R32_RTC_CNT_32K_ADDR  0x40001038u
/* Hop-clock modulus: RF_PROTO_HOP_WRAP from rf_protocol.h (single source —
 * a local duplicate here once risked drifting from the shared hop stepper). */

/* R32_RTC_CNT_32K crosses from the asynchronous 32 kHz clock domain; a
 * single in-flight read can capture a torn value. Observed on this board
 * (2026-07-05, P3b logger, 2.06M samples): +2880-tick (+90 ms) forward
 * jumps at ~7e-6 per read, punching through supervision deltas and the
 * phase-error buckets. Read until two consecutive loads agree — the
 * vendor's own RTC_GetCycle32k (CH59x_clk.c) shape. Converges in 1-2
 * iterations: back-to-back loads are ~130 ns apart vs the 31.25 us tick.
 * Called from the radio-IRQ tail too: on healthy hardware this converges
 * in 0-1 retries (sub-microsecond); like the vendor loop it has no
 * iteration cap, so a counter that never produced two equal consecutive
 * reads (broken oscillator/peripheral) would spin — a hardware-failure
 * mode, not a software path. */
static inline uint32_t rtc_read_32k(void)
{
    uint32_t v = *(volatile uint32_t *)R32_RTC_CNT_32K_ADDR;

    for (;;) {
        uint32_t v2 = *(volatile uint32_t *)R32_RTC_CNT_32K_ADDR;

        if (v2 == v) {
            break;
        }
        v = v2;
    }
    return v;
}

static inline uint32_t rtc_delta_32k(uint32_t now, uint32_t last)
{
    return rf_supervision_wrapped_delta(now, last, RF_PROTO_HOP_WRAP,
                                        RF_RTC_BACKSTEP_TOLERANCE_TICKS);
}

/* Entropy for the session-AA RNG seed: the async RTC domain adds true jitter
 * on CH59x; the CH570 (no such register) uses the free-running Tsys tick. */
#define RF_ENTROPY_TICKS() rtc_read_32k()
#else
#define RF_ENTROPY_TICKS() hal_now()
#endif /* RF_TASK_EXECUTOR_TMOS */

/* ---------- Hop clock (P3b iii-b) ----------
 *
 * The channel-hop grid is anchored and stepped in protocol ticks of 1/32000 s
 * (the "32K" clock rate is the LSI's calibration target CAB_LSIFQ=32000, NOT
 * 32768 Hz), read from an HSE-derived software counter: one protocol tick =
 * exactly 1875 Tsys ticks at 60 MHz, accumulated from modular hal_now()
 * deltas with a sub-tick remainder, and WRAPPED AT THE SAME 0xA8C00000
 * MODULUS as the RTC counter -- so rtc_delta_32k, the repeat-correction wrap
 * branch and every existing anchor computation work unchanged.
 *
 * The RTC32K/LSI fallback (RF_HOP_ANCHOR_HSE=0, the stock shape) was retired
 * in the unify-rf-task P1b pass after the P3b gate campaign closed on the HSE
 * anchor: ~16M samples across cold/warm/fault/load/2h-soak conditions, zero
 * >=100 us per-interval RTC-vs-HSE disagreement vs the ~875 us RX window,
 * while the LSI itself wandered -27..-526 ppm with thermal state -- the
 * variability the switch removed (analysis/p3b-gate-evidence-2026-07-05.md).
 * The keyboard side runs a per-RX phase servo (PROTOCOL.md:824), so
 * CONNECTED is closed-loop.
 *
 * Liveness: modular hal_now() deltas are valid only under the 71.6 s SysTick
 * wrap. rf_hop_read() is called from every poll (CONNECTED), every pair-prep
 * rotation (PAIRING/EV10 scan -- see the keepalive in rf_send_pair_prep), and
 * the promote/seed sites, so consecutive reads stay far below the wrap while
 * any hop timestamp is live. Across a LONG camped idle (bonded, keyboard off,
 * no pair traffic) the absolute counter may alias -- harmlessly: every
 * consumer uses deltas between reads that both happen after re-acquisition
 * re-seeds the anchors (no live timestamp spans the gap).
 *
 * Context: called from BOTH the radio-IRQ event sink (promote/seed sites) and
 * TMOS task context (rf_send_poll), so the counter update runs in a short
 * CSR-0x800 critical section (the same save/restore idiom usb_device.c uses;
 * no PFIC helpers, no RF/TMOS calls inside). u32-only arithmetic -- no
 * 64-bit soft-division on the IRQ path. */

static uint32_t rf_hop_hse_ticks;    /* protocol ticks, mod RF_PROTO_HOP_WRAP */
static uint32_t rf_hop_hse_last;     /* hal_now() at the last update */
static uint32_t rf_hop_hse_rem;      /* sub-tick Tsys remainder (0..1874) */
static uint8_t  rf_hop_hse_started;

__HIGH_CODE
static uint32_t rf_hop_read(void)
{
    uint32_t irq = __risc_v_disable_irq();
    uint32_t now = hal_now();
    uint32_t ticks;

    if (!rf_hop_hse_started) {
        rf_hop_hse_started = 1;
        rf_hop_hse_last = now;
    } else {
        uint32_t d = now - rf_hop_hse_last;          /* modular, < 71.6 s */
        uint32_t q = d / HAL_TICKS_PER_PROTO_TICK;
        uint32_t r = d - q * HAL_TICKS_PER_PROTO_TICK;
        uint32_t t;

        rf_hop_hse_last = now;
        rf_hop_hse_rem += r;                         /* < 2*1875: no overflow */
        if (rf_hop_hse_rem >= HAL_TICKS_PER_PROTO_TICK) {
            rf_hop_hse_rem -= HAL_TICKS_PER_PROTO_TICK;
            q++;
        }
        t = rf_hop_hse_ticks + q;                    /* < WRAP + 2.3e6: no overflow */
        if (t >= RF_PROTO_HOP_WRAP) {
            t -= RF_PROTO_HOP_WRAP;
        }
        rf_hop_hse_ticks = t;
    }
    ticks = rf_hop_hse_ticks;
    __risc_v_enable_irq(irq);
    return ticks;
}

/* Wrap-safe backdate on the hop clock's modulus (codex: never leave a raw
 * `- 13` that can underflow past zero near the wrap). always_inline makes the
 * no-call-from-IRQ contract explicit (callers include the radio-IRQ sink). */
__attribute__((always_inline))
static inline uint32_t rf_hop_backdate(uint32_t t, uint32_t ticks)
{
    return (t >= ticks) ? (t - ticks) : (t + RF_PROTO_HOP_WRAP - ticks);
}

/* Timestamp of the last CONNECTED-state RX, in hal_now() Tsys ticks (P3a —
 * supervision lapse measurement moved off RTC32K; deltas are plain 2^32
 * modular subtraction: stamps refresh every connected RX and every read
 * happens within the 10 s supervision deadline, far under the 71.6 s wrap).
 * 0 = no RX this session (the 1-in-2^32 hal_now()==0 stamp collision merely
 * defers supervision by one RX — same sentinel semantics as the old RTC
 * form). Written from the radio IRQ-tail sink, read from task context. */
static volatile uint32_t rf_last_conn_rx_tsys;

/* OQ7 Track 2d: stock dongle's event-0x02 channel hop formula state.
 * Hoisted here (file-scope) because both the burst-promote branch
 * and rf_send_poll use it. See implementation in rf_send_poll. */



/* The shared stock hop state (rf_protocol.h). Field semantics identical to
 * the old stock_last_rtc/stock_prev_idx pair; writes happen in both the
 * radio-IRQ sink (seed sites) and task context (per-poll step), same as
 * before -- the formula itself runs only in task context (rf_send_poll). */
static volatile rf_proto_hop_t rf_hop;
static volatile uint8_t  stock_seed_burst_applied;

/* RF_STOCK_PROMOTE_SEED: reconnect A/B knob. A 2026-05-22 live stock
 * single-step trace at firmware.bin runtime 0x20000f8c and EMU-Dongle
 * exp58 showed the first connected poll entering the hop formula with
 * prev_idx=2, elapsed=0x1d, interval=0x1c, producing idx=3 -> channel 28.
 * Keep the stock first-hop shape by default. With early burst promotion this
 * no longer papers over the old six-burst delay; it only preserves the stock
 * first-poll checkpoint while TMR0 starts at the state-1 TX-finish boundary. */

/* ---------- Forward declarations ---------- */

static void rf_start_rx(void);
static void rf_rearm_rx(void);
#if DONGLE_RX_WINDOW
static void rf_win_reset(void);
#endif
static void rf_configure(uint32_t access_addr);
static void rf_send_poll(void);
static void rf_send_pair_prep(void);
static void rf_send_pair_ack(void);
static void rf_request_bond_persist(void);
static void rf_persist_bond_task(void);
#if RF_CONFIRM_BEFORE_PERSIST
static void rf_commit_bond_ram(void);
static void rf_arm_bond_persist(void);
#endif

/* Pair-accept peer-MAC guard (V2 zero-MAC; widened by N08/GB5: all-FF is
 * jam/garbage, and a peer equal to OUR OWN advertised identity would
 * air-persist a record the boot validator then rejects — re-pair every boot
 * — so it must never be accepted in the first place). On CH570 the accept
 * sites live in the __HIGH_CODE radio-IRQ sink and the product sits against
 * the 2 KB stack-floor assert, so keep the check flash-resident (a call, not
 * an inline body — same precedent as rf_return_to_fresh_pair /
 * rf_test_synth_hid_tick). On CH59x (TMOS, ample SRAM) inline it. */
#if !RF_TASK_EXECUTOR_TMOS
__attribute__((noinline))
static uint8_t rf_accept_peer_mac(const uint8_t *mac)
{
    return (uint8_t)(rf_proto_mac_nonzero(mac) && !rf_proto_mac_all_ff(mac)
                     && !rf_proto_mac_equal(mac, rf_bond_dongle_mac));
}
/* Review finding D6: clear the boot bond-persist latch when a boot-window
 * accept CHANGES the peer MAC (new keyboard), so the promote persists the new
 * bond; a same-peer reconnect (MAC equal) leaves the latch set (CX4 — no
 * redundant flash write). Flash-resident noinline: the sole caller is the
 * __HIGH_CODE radio-IRQ accept site and the product sits against the 2 KB
 * stack-floor assert (same precedent as rf_accept_peer_mac). tmos_memcmp
 * is TRUE-when-equal, so !tmos_memcmp == changed. */
__attribute__((noinline))
static void rf_relatch_bond_on_peer_change(const uint8_t *newmac)
{
    if (!tmos_memcmp(rf_peer_mac, newmac, 6)) {
        rf_bond_persisted = 0;
    }
}
#else
static inline uint8_t rf_accept_peer_mac(const uint8_t *mac)
{
    return (uint8_t)(rf_proto_mac_nonzero(mac) && !rf_proto_mac_all_ff(mac)
                     && !rf_proto_mac_equal(mac, rf_bond_dongle_mac));
}
#endif

/* hal_timing CONNECTED_POLL slot callback: adapts the seam's cb(slot) signature
 * to the existing connected poll. Dispatched in TMOS task context (CH59x cannot
 * run RF calls from a timer ISR). Passed to hal_timer_arm() at the connected-poll
 * arm sites; the seam stores it for the P2.5 shared-rf_task dispatch (the CH592
 * connected poll still dispatches natively via RF_EVT_POLL this increment). */
#if !RF_TASK_EXECUTOR_TMOS
/* Promote-time acquisition arm (option-C note at the top of the file):
 * snapshot the connected-RX tally the sweep freezes on, and on the FIRST
 * session seed the fixed v0.96-derived offset. rf_ch570_acq_nudges survives
 * re-promotes as accepted-request TELEMETRY/wrap bookkeeping — NOT as
 * cross-session physical phase: this arm never converts the counter back into
 * grid phase, and every promote re-anchors the physical grid (fresh via
 * st_set_periodic ALL_CLEAR; EV10 inherits the freshly-anchored pair-ACK
 * grid). So the "cumulative cross-session tiling" the older comments claimed
 * is NOT implemented (CODEREVIEW N10, accepted residual — the stock Bridge75
 * is production-validated regardless; a true cumulative-phase primitive is
 * deferred pending a phase-controllable failing control, see
 * analysis/codex-review-campaign-2026-07-17/change12-N10-sweep-spike.md).
 * Flash-resident noinline: the promote paths run in the HIGH_CODE sink (SRAM). */
__attribute__((noinline))
static void rf_ch570_acq_arm(uint8_t seed)
{
    rf_ch570_acq_base = rf_ch570_connected_rx_count;
    if (seed && rf_ch570_acq_nudges == 0u) {
        (void)hal_timer_grid_nudge(RF_CH570_GRID_PHASE_OFFSET_TICKS);
    }
}
#endif

static void rf_connected_poll_cb(uint8_t slot)
{
    (void)slot;
    if (rf_quiesced) {
        return;
    }
    rf_send_poll();
#if !RF_TASK_EXECUTOR_TMOS
    /* Phase-acquisition sweep (see the option-C note at the top of the
     * file): while CONNECTED with zero poll responses this session, walk
     * the grid +8 us per poll until the sleeping keyboard's narrow RX
     * window answers; first reply freezes the grid (flat from then on —
     * the keyboard's per-packet servo holds it). Runs after the TX so the
     * stretch applies to the NEXT period; the primitive self-guards
     * (early-cycle only, one pending stretch). */
    if (rf_state == RF_STATE_CONNECTED &&
        rf_ch570_connected_rx_count == rf_ch570_acq_base) {
        /* Within ONE uninterrupted grid the sweep walks +8 us/poll from the
         * ownership-entry phase; the first reply freezes it (the keyboard's
         * per-packet servo then holds it). N10 CAVEAT: this is a LOCAL sweep —
         * a ~26-poll session covers only ~0..267 us of the 875 us stock slot
         * (requests are pipelined: the shift lands one cycle late, so the last
         * ~2 accepted steps are not yet on a transmitted poll at teardown),
         * and the counter below does NOT carry physical phase into the next
         * (re-anchored) session, so consecutive sessions re-walk substantially
         * the SAME band. The stock Bridge75 still locks (jitter + the differing
         * fresh/EV10 anchor bases reach its window in practice), but full-slot
         * cross-session coverage is NOT achieved. See rf_ch570_acq_arm (N10). */
        if (rf_ch570_acq_nudges >= RF_CH570_ACQ_MAX_NUDGES) {
            rf_ch570_acq_nudges = 0u;   /* wrap the telemetry counter (accepted
                                         * requests), not a physical slot walk */
        }
        if (hal_timer_grid_nudge(RF_CH570_ACQ_STEP_TICKS)) {
            rf_ch570_acq_nudges++;      /* accepted steps only */
        }
    }
#endif
}

/* PAIR_ACK slot callback (P2.3 ii-b): paces the 15-byte pair-completion TX.
 * Same shim shape as rf_connected_poll_cb — the seam stores it for the P2.5
 * shared-rf_task dispatch; this increment the pair-ACK still dispatches
 * natively via TMR0_IRQHandler → RF_EVT_SEND_PAIR_ACK in task context. */
static void rf_pair_ack_cb(uint8_t slot)
{
    (void)slot;
    if (rf_quiesced) {
        return;
    }
    rf_send_pair_ack();
}

/* EV10_REKEY / BOOT_WINDOW slot callbacks (P2.3 ii): on CH59x these slots are
 * TMOS-timer-backed (625 us TMOS units until P3a moves the deadlines onto
 * Tsys/hal_now). The cbs just post the same TMOS event the expiring timer
 * would, so a future seam-side dispatch is behavior-identical. */
static void rf_ev10_rekey_cb(uint8_t slot)
{
    (void)slot;
    hal_event_post(RF_EVT_TIMEOUT);
}

static void rf_boot_window_cb(uint8_t slot)
{
    (void)slot;
    hal_event_post(RF_EVT_BOOT_WINDOW);
}

/* TMOS deadline primitives the CH592 seam fronts for those two slots (the
 * seam cannot reach rf_taskID / the RF_EVT_* bits itself). NOTE the
 * transitional unit divergence from hal_timing.h's Tsys contract: these two
 * slots take 625 us TMOS units on CH592 until P3a. */
#if RF_TASK_EXECUTOR_TMOS
/* A port that tracks app deadlines (CH592 exact-deadline heartbeat,
 * hal_timing_ch592.h) redirects these two pairs; the default is the bare
 * TMOS call. These, plus hal_event_post_delayed / hal_event_cancel, are
 * every timer start and stop for rf_taskID. */
#ifndef RF_TMOS_START
#define RF_TMOS_START(bit, units) tmos_start_task(rf_taskID, (bit), (units))
#define RF_TMOS_STOP(bit)         tmos_stop_task(rf_taskID, (bit))
#endif
void rf_ev10_deadline_start(uint32_t tmos_ticks)
{
    RF_TMOS_START(RF_EVT_TIMEOUT, tmos_ticks);
}

void rf_ev10_deadline_stop(void)
{
    RF_TMOS_STOP(RF_EVT_TIMEOUT);
}

void rf_boot_window_deadline_start(uint32_t tmos_ticks)
{
    RF_TMOS_START(RF_EVT_BOOT_WINDOW, tmos_ticks);
}

void rf_boot_window_deadline_stop(void)
{
    RF_TMOS_STOP(RF_EVT_BOOT_WINDOW);
}
#endif /* RF_TASK_EXECUTOR_TMOS — the CH570 hal_timing serves these slots
        * natively (st_set/st_cancel); no rf_task-provided backing needed. */

static uint16_t rf_active_conn_interval(void)
{
    uint16_t interval = rf_conn_interval;

    if (interval == 0) {
        interval = rf_protocol_pair_ack_interval(rf_pair_ack15);
    }
    return rf_supervision_conn_interval_or_default(interval);
}

static uint16_t rf_active_conn_timeout(void)
{
    uint16_t timeout = rf_conn_timeout;

    if (timeout == 0) {
        timeout = rf_protocol_pair_ack_timeout(rf_pair_ack15);
    }
    return rf_supervision_conn_timeout_or_default(timeout);
}

static uint32_t rf_connected_supervision_ticks(uint8_t first_arm)
{
    uint16_t tmos = first_arm
                  ? rf_supervision_stock_first_tmos(rf_active_conn_interval())
                  : rf_supervision_stock_timeout_tmos(rf_active_conn_timeout());

    rf_stock_first_supervision_armed = first_arm ? 1u : 0u;
    return (uint32_t)tmos * HAL_TMOS_UNIT_TICKS;
}

static void rf_arm_connected_supervision(uint8_t first_arm)
{
    uint32_t ticks = rf_connected_supervision_ticks(first_arm);

    hal_timer_cancel(HAL_TMR_SLOT_EV10_REKEY);
    hal_timer_arm(HAL_TMR_SLOT_EV10_REKEY, ticks, rf_ev10_rekey_cb);
}

/* Per-packet supervision refresh from the radio IRQ-tail RX sink (~1143/s on a
 * connected link). Arm-only: the same-slot restart replaces the deadline in
 * place, so skipping the hal_timer_cancel avoids a TMOS timer-node free+alloc
 * on every connected RX. A stale RF_EVT_TIMEOUT that slips past (the cancel
 * would otherwise have drained it) lands in the healthy-link grace path and
 * benignly re-arms — the EV10-entry sites, where the drained event is
 * load-bearing, keep their explicit cancel+arm. */
static void rf_refresh_connected_supervision(void)
{
    hal_timer_arm(HAL_TMR_SLOT_EV10_REKEY,
                  rf_connected_supervision_ticks(0), rf_ev10_rekey_cb);
}

static void rf_send_keys_up_on_link_loss(void)
{
    if (rf_state != RF_STATE_CONNECTED || !rf_hid_callback) {
        return;
    }
    /* Always drop any wake-time key-DOWN stash first: the keyboard is gone, so
     * no matching key-up is coming, and the resume flush must not replay it as
     * a stuck key (CODEREVIEW P2). This covers the case where link loss is
     * detected while still suspended (the common path) AND the narrow window
     * where the host has just resumed but the stash is not yet flushed. */
    USB_ClearPendingKeyboard();
    if (USB_IsSuspended()) {
        /* Host asleep: do NOT push keys-up through the normal send path -- that
         * would call usb_hid_in_ready() and request a spurious remote wake for a
         * keyboard that merely died. The stash is already neutralized above, so
         * the eventual resume flush emits an explicit all-keys-up on its own. */
        return;
    }
    static const uint8_t keys_up[8] = { 0 };
    rf_hid_callback(RF_PROTO_HID_TAG, keys_up, sizeof(keys_up));
}

/* Abort any in-flight pair-ACK burst chain: clear the FSM latch and cancel the
 * delayed chain step so a state transition (TX fail, supervision teardown)
 * can't leave a stale burst that later resurrects on an unrelated TX_FINISH or
 * fires TX_PAIR_15B onto a wrong channel/AA. Safe to call when no burst is
 * active. */
static void rf_abort_pair_burst(void)
{
    rf_inject_burst_active = 0;
    rf_inject_burst_idx    = 0;
    hal_event_cancel(RF_EVT_TX_PAIR_15B);
}

/* Fresh-pair fallback (SHARED across executors as of the CH59x P1/P4 port). On
 * CH570 the caller is the unconfirmed-pair tally check in rf_enter_stock_reacquire;
 * on CH59x it is the P1 pair-ACK-TX recovery. The ACTION below (re-camp the
 * boot-window relisten) is identical; only the DETECTION differs per executor.
 *
 * Unconfirmed fresh pair: the CONNECTED tallies are still zero for this boot,
 * so no keyboard has EVER exchanged a connected frame with us — the promote
 * came purely from our own pair-ACK TX_FINISHes and the keyboard never
 * confirmed the ACK (bench-reproduced 2026-07-07 with mangled-ACK fault
 * injection). Two sub-cases, indistinguishable from here: it heard NOTHING
 * (still pair-broadcasting on the PAIR AA — which no session-AA scan or camp
 * can ever hear), or it heard only the first ACK (stored our AA+MAC as a
 * bond, then reconnect-broadcasts on the SESSION AA). Re-run the stock
 * boot-window alternation, which listens on both AAs; the known-peer accept
 * (the bond carries the keyboard's MAC from the failed attempt) completes
 * either path without opening the pair window to other keyboards. If the
 * keyboard is gone, the window expiry settles on the session-AA reconnect
 * camp — the pre-fix terminal state. Repeated failures re-enter here on each
 * unconfirmed promote, so the retry loop sustains while the keyboard keeps
 * broadcasting. (Detection reads the always-on rf_ch570_len1/len10 tallies
 * from task context — deliberately NOT a per-promote latch in the radio-IRQ
 * sink: the sink is __HIGH_CODE and CH570 SRAM sits against the 2 KB
 * stack-floor assert. Consequence: after any CONFIRMED link this boot, a
 * later failed re-pair takes the old reacquire path — acceptable, since a
 * new-keyboard pair needs a replug boot window anyway.) */
static void rf_return_to_fresh_pair(void)
{
    rfd_fresh_relistens++;
    hal_timer_cancel(HAL_TMR_SLOT_CONNECTED_POLL);
    hal_timer_cancel(HAL_TMR_SLOT_PAIR_ACK);
    hal_timer_cancel(HAL_TMR_SLOT_EV10_REKEY);
    hal_event_cancel(RF_EVT_PAIR_PREP);
    hal_event_cancel(RF_EVT_SEND_PAIR_ACK);
    hal_event_cancel(RF_EVT_POLL);
    hal_event_cancel(RF_EVT_POST_POLL_RX);
    rf_abort_pair_burst();
#if RF_CONFIRM_BEFORE_PERSIST
    /* N11: clear the per-attempt confirm state (NOT rf_bond_persisted/rf_bond_valid
     * — the tentative peer is kept so the relisten retries the SAME keyboard; the
     * rf_bond_persisted clear for a genuinely tentative WAIT_RX pair stays at the
     * confirm-timeout site, since this helper is also the good-bond relisten path). */
    rf_confirm_state = RF_CONFIRM_STATE_NONE;
    hal_event_cancel(RF_EVT_CONFIRM_TIMEOUT);
#endif
#if RF_TASK_EXECUTOR_TMOS
    rf_burst_txfail_fallback = 0u;   /* consumed with this attempt */
#endif

    rf_supervision_ev10_active = 0;
    rf_stock_first_supervision_armed = 0;
    rf_last_conn_rx_tsys = 0;

    rf_boot_window_active = 1u;
    rf_pair_window_open   = 0u;
    rf_boot_window_step   = 0u;
#if DONGLE_RX_WINDOW
    rf_win_reset();
#endif
    rf_camp_wd_active     = 0u;   /* the window takes the slot back; its close re-arms the watchdog */
    rf_state = RF_STATE_PAIRING;
    rf_access_addr = rf_bond_aa;
    rf_channel = RF_PROTO_RECONNECT_CAMP_CHANNEL;
    rf_start_rx();
    hal_timer_arm(HAL_TMR_SLOT_BOOT_WINDOW, RF_BOOT_WINDOW_TICKS_TSYS,
                  rf_boot_window_cb);
    
}

#if DONGLE_RX_WINDOW
/* ---------- Tier 2 R1: windowed receiver (CH592) ----------
 * Against a resting production keyboard the dongle spent ~990 ms of every
 * second in the reacquire scan to catch a ~10 ms probe that arrives once per
 * second (1.010 s, sd 15 ms); against an absent keyboard the camp kept RX on
 * for nothing. The receiver is ~7 mA of the dongle's draw. Windowing keeps
 * the radio shut between short receiver windows:
 *   - the scan's PAIR_PREP arm is the window open (channel 8 only: the
 *     production probe sweeps all three pairing channels inside its ~10 ms,
 *     measured 2026-09-10 with the scan pinned to each), RF_EVT_RX_WIN_CLOSE
 *     shuts the radio W ms later unless a beacon was accepted meanwhile, and
 *     the next open follows at P - W;
 *   - once the scheduled-drop detector is locked (confirmed traffic on a
 *     link no longer than 2 s of grid periods, a drop within 300 ms of the
 *     promote, twice at ~1 s cadence) one window per
 *     second is phase-locked to the predicted probe (RF_EVT_RX_WIN_PHASE);
 *     a miss widens the next one, two misses fall back to the continuous
 *     scan until the next promote, because the keyboard's THIRD unanswered
 *     probe sends it to a sleep stage its host must end;
 *   - the terminal camp's 200 ms tick becomes the window open, period P;
 *   - a grace period keeps today's continuous receiver for the first T
 *     seconds after a scheduled drop (the first key after a short pause
 *     keeps its 40 ms), counted in probe cycles in the scan and in ticks in
 *     the camp.
 * Acceptance inside a window hands the radio to the existing accept path
 * (300 us PAIR_ACK slot, 15-byte ACK, promote) untouched: the close handler
 * checks ownership under the IRQ mask and does nothing once the state moved
 * on. Everything here is task context except rf_win_on_promote (radio sink)
 * and the answered-poll count (connected RX sink). */
#ifndef DONGLE_RX_WINDOW_MS
#define DONGLE_RX_WINDOW_MS 30u
#endif
#ifndef DONGLE_RX_PERIOD_MS
#define DONGLE_RX_PERIOD_MS 200u
#endif
#ifndef DONGLE_RX_GRACE_S
#define DONGLE_RX_GRACE_S 60u
#endif
#ifndef DONGLE_RX_PHASE_MS
#define DONGLE_RX_PHASE_MS 120u
#endif
#if DONGLE_RX_WINDOW_MS < 10 || DONGLE_RX_WINDOW_MS >= DONGLE_RX_PERIOD_MS \
    || DONGLE_RX_PHASE_MS < DONGLE_RX_WINDOW_MS || DONGLE_RX_PHASE_MS > DONGLE_RX_PERIOD_MS * 5u
#error "DONGLE_RX_WINDOW_MS/PERIOD_MS/PHASE_MS: need 10 <= W < P and W <= PHASE <= 5*P"
#endif
#define RF_WIN_MS_TO_TICKS(ms)   ((uint32_t)(ms) * 1000u * HAL_TICKS_PER_US)
#define RF_WIN_PROBE_PERIOD_MS   1010u   /* measured resting-probe period */
#define RF_WIN_PHASE_LEAD_MS     45u     /* 3 sigma of the measured jitter (15 ms) */
#define RF_WIN_PHASE_WIDEN_MS    15u     /* per miss */
#define RF_WIN_MAX_MISSES        2u      /* the third probe must be caught continuously */
#define RF_WIN_MIN_LINK_RX       1u      /* answered polls that make a drop "confirmed traffic": the keyboard was on the
                                          * data channel (a failed acquisition answers none; a ~10 ms resting link 4-11,
                                          * occasionally fewer); the lock still needs two such drops at the 1 s cadence */
#define RF_WIN_MAX_LINK_TICKS    64000u  /* TMR0 periods elapsed on the link times the negotiated interval, in hop
                                          * ticks of 31.25 us: 2 s. An elapsed-time bound from the dongle's own poll
                                          * grid, so a qualifying link cannot have wrapped hal_now() (71.6 s) at
                                          * ANY advertised interval; a resting burst is well under it */
#define RF_WIN_DROP_MAX_MS       300u    /* promote -> lapse within this = a scheduled drop (the lapse dispatch can
                                          * trail the keyboard's ~10 ms stop by the supervision timeout plus a busy
                                          * foreground, e.g. the library's 1 s ADC sample) */
#define RF_WIN_CADENCE_MIN_MS    900u
#define RF_WIN_CADENCE_MAX_MS    1100u
#define RF_WIN_CAMP_TICK_MS      200u    /* RF_CAMP_WD_TICKS_TSYS */

static uint8_t  rf_win_mode;             /* 1 = windowed: radio shut between windows */
static uint8_t  rf_win_open;             /* a window is armed */
static uint8_t  rf_win_phase_open;       /* the open window is the phase window */
static uint8_t  rf_win_locked;           /* scheduled-drop detector locked on a resting keyboard */
static uint8_t  rf_win_misses;           /* consecutive phase-window misses */
static uint8_t  rf_win_sched_runs;       /* consecutive scheduled drops (saturating at 2): the lock needs two */
static volatile uint8_t rf_win_accepted; /* the radio sink accepted a beacon inside the current window (ownership passed) */
static uint8_t  rf_win_fault_next;       /* rung 3 while windowed: the next open arms, then shuts (deaf) */
static uint32_t rf_win_grace_ms = (uint32_t)DONGLE_RX_GRACE_S * 1000u;   /* grace remaining before windowing engages */
static uint16_t rf_win_phase_ms;         /* current phase window width */
static volatile uint16_t rf_win_link_rx; /* answered polls on the current link (connected RX sink) */
static volatile uint32_t rf_win_link_periods; /* TMR0 grid periods elapsed on the current link (the CYC_END ISR, once per
                                               * period whether or not the task loop coalesces the poll events), saturating */
static uint32_t rf_win_promote_tsys, rf_win_prev_promote_tsys;
static volatile uint32_t rfd_win_opens, rfd_win_closes, rfd_win_phase_opens, rfd_win_phase_misses;
static volatile uint32_t rfd_win_catches, rfd_win_locks, rfd_win_unlocks, rfd_win_engages, rfd_win_faults;
static uint8_t rfd_win_unsched_rx, rfd_win_unsched_long, rfd_win_unsched_late, rfd_win_uncadenced;   /* why a drop did not qualify */

static uint8_t rf_camp_is_terminal(void);
static void rf_arm_retry_if_failed(void);
static void rf_ev10_rekey_cb(uint8_t slot);
static void rfd_put32(uint8_t *p, uint32_t v);
static void rfd_put16(uint8_t *p, uint16_t v);

static void rf_win_reset(void)
{
    hal_event_cancel(RF_EVT_RX_WIN_CLOSE);
    hal_event_cancel(RF_EVT_RX_WIN_PHASE);
    rf_win_mode = 0u; rf_win_open = 0u; rf_win_phase_open = 0u; rf_win_locked = 0u;
    rf_win_misses = 0u; rf_win_sched_runs = 0u; rf_win_accepted = 0u; rf_win_fault_next = 0u;
    rf_win_grace_ms = (uint32_t)DONGLE_RX_GRACE_S * 1000u;
    rf_win_phase_ms = (uint16_t)DONGLE_RX_PHASE_MS;
}

/* Promote (radio sink, IRQ tail): the link is up; no window may fire. */
__HIGH_CODE
static void rf_win_on_promote(void)
{
    hal_event_cancel(RF_EVT_RX_WIN_CLOSE);
    hal_event_cancel(RF_EVT_RX_WIN_PHASE);
    if (rf_win_open) {
        rf_win_open = 0u; rf_win_phase_open = 0u; rfd_win_catches++;
    }
    rf_win_prev_promote_tsys = rf_win_promote_tsys;
    rf_win_promote_tsys = hal_now();
    rf_win_accepted = 0u;
    rf_win_link_rx = 0u;
    rf_win_link_periods = 0u;
    rf_win_misses = 0u;
    rf_win_phase_ms = (uint16_t)DONGLE_RX_PHASE_MS;
}

/* Supervision lapse (task, before the scan starts): the scheduled-drop detector. */
static void rf_win_on_lapse(void)
{
    uint32_t now = hal_now();
    uint32_t since_promote = now - rf_win_promote_tsys;                      /* modular Tsys */
    uint32_t cadence = rf_win_promote_tsys - rf_win_prev_promote_tsys;        /* modular Tsys */
    uint32_t interval = (rf_conn_interval != 0u) ? rf_conn_interval : 1u;
    uint8_t short_link = (uint8_t)(rf_win_link_periods <= RF_WIN_MAX_LINK_TICKS / interval);
    uint8_t scheduled = (uint8_t)(rf_win_link_rx >= RF_WIN_MIN_LINK_RX && short_link
                                  && since_promote < RF_WIN_MS_TO_TICKS(RF_WIN_DROP_MAX_MS));
    if (rf_win_link_rx < RF_WIN_MIN_LINK_RX) { rfd_win_unsched_rx++; }
    else if (!short_link) { rfd_win_unsched_long++; }
    else if (since_promote >= RF_WIN_MS_TO_TICKS(RF_WIN_DROP_MAX_MS)) { rfd_win_unsched_late++; }
    uint8_t cadenced = (uint8_t)(rf_win_sched_runs >= 1u
                                 && cadence >= RF_WIN_MS_TO_TICKS(RF_WIN_CADENCE_MIN_MS)
                                 && cadence <= RF_WIN_MS_TO_TICKS(RF_WIN_CADENCE_MAX_MS));

    hal_event_cancel(RF_EVT_RX_WIN_CLOSE);
    hal_event_cancel(RF_EVT_RX_WIN_PHASE);
    hal_event_cancel(RF_EVT_RX_RESTART);
    rf_win_open = 0u; rf_win_phase_open = 0u; rf_win_accepted = 0u;
    if (scheduled) {
        if (rf_win_sched_runs < 2u) { rf_win_sched_runs++; }
    } else {
        rf_win_sched_runs = 0u;
    }
    if (scheduled && !cadenced && rf_win_sched_runs >= 2u) { rfd_win_uncadenced++; }
    if (scheduled && cadenced) {
        /* two consecutive scheduled drops ~1 s apart: a resting production keyboard */
        if (!rf_win_locked) { rf_win_locked = 1u; rf_win_misses = 0u; rfd_win_locks++; }
        if (!rf_win_mode) {
            if (rf_win_grace_ms > RF_WIN_PROBE_PERIOD_MS) {
                rf_win_grace_ms -= RF_WIN_PROBE_PERIOD_MS;
            } else {
                rf_win_grace_ms = 0u; rf_win_mode = 1u; rfd_win_engages++;
            }
        }
    } else {
        /* an unscheduled loss, or the cadence broke: today's continuous scan. The grace
         * is replenished only by a genuine session (a link past the grid bound: the user
         * was typing); a short drop that merely missed the traffic or timing test is
         * still the resting signature and must not keep restarting the grace. */
        if (rf_win_locked) { rf_win_locked = 0u; rfd_win_unlocks++; }
        if (!short_link) { rf_win_grace_ms = (uint32_t)DONGLE_RX_GRACE_S * 1000u; }
        rf_win_mode = 0u;
    }
    if (rf_win_mode && rf_win_locked) {
        uint32_t since_ms = since_promote / RF_WIN_MS_TO_TICKS(1u);
        uint32_t open_at_ms = RF_WIN_PROBE_PERIOD_MS - RF_WIN_PHASE_LEAD_MS;
        uint32_t delay_ms = (since_ms + DONGLE_RX_WINDOW_MS < open_at_ms) ? (open_at_ms - since_ms) : DONGLE_RX_WINDOW_MS;
        hal_event_post_delayed(RF_EVT_RX_WIN_PHASE, RF_WIN_MS_TO_TICKS(delay_ms));
    }
}

/* RF_EVT_RX_WIN_PHASE (task): open the phase-locked window in the scan. */
static void rf_win_phase_open_now(void)
{
    if (!rf_win_mode || !rf_win_locked || !rf_supervision_ev10_active || rf_state != RF_STATE_PAIRING) {
        return;
    }
    hal_event_cancel(RF_EVT_PAIR_PREP);      /* the 5 Hz open yields to the phase window */
    hal_event_cancel(RF_EVT_RX_WIN_CLOSE);
    rf_win_phase_open = 1u;
    rfd_win_phase_opens++;
    rf_send_pair_prep();                     /* arms channel 8 and posts the close at the phase width */
}

/* RF_EVT_RX_WIN_CLOSE (task): shut the radio unless the window's state moved on. */
static void rf_win_close(void)
{
    uint32_t irq = __risc_v_disable_irq();
    uint8_t in_scan = (uint8_t)(rf_supervision_ev10_active && rf_state == RF_STATE_PAIRING);
    uint8_t in_camp = (uint8_t)(rf_camp_wd_active && rf_camp_is_terminal());
    uint8_t owned = (uint8_t)(rf_win_open && rf_win_mode && !rf_win_accepted && (in_scan || in_camp));
    uint8_t was_phase = rf_win_phase_open;

    if (owned) {
        hal_event_cancel(RF_EVT_RX_RESTART);   /* a failed-arm retry must not reopen a closed window */
        hal_rf_shut();
    }
    rf_win_open = 0u; rf_win_phase_open = 0u;
    (void)__risc_v_enable_irq(irq);
    if (!owned) {
        return;                              /* accepted meanwhile, or the state moved on */
    }
    rfd_win_closes++;
    if (in_scan) {
        if (was_phase) {
            rfd_win_phase_misses++;
            rf_win_misses++;
            /* keep the scan alive across the miss instead of giving up to the camp
             * (drain a coalesced timeout first: rf_ev10_rekey_cb posts RF_EVT_TIMEOUT) */
            hal_event_cancel(RF_EVT_TIMEOUT);
            hal_timer_arm(HAL_TMR_SLOT_EV10_REKEY,
                          RF_SUPERVISION_STOCK_WATCHDOG_TMOS * HAL_TMOS_UNIT_TICKS, rf_ev10_rekey_cb);
            if (rf_win_misses >= RF_WIN_MAX_MISSES) {
                rf_win_mode = 0u;            /* continuous scan until the next promote re-locks */
                hal_event_post(RF_EVT_PAIR_PREP);
                return;
            }
            rf_win_phase_ms = (uint16_t)(rf_win_phase_ms + RF_WIN_PHASE_WIDEN_MS);
            hal_event_post_delayed(RF_EVT_RX_WIN_PHASE,
                                   RF_WIN_MS_TO_TICKS(RF_WIN_PROBE_PERIOD_MS - rf_win_phase_ms));
        }
        hal_event_post_delayed(RF_EVT_PAIR_PREP,
                               RF_WIN_MS_TO_TICKS(DONGLE_RX_PERIOD_MS - DONGLE_RX_WINDOW_MS));
    }
    /* camp: the camp tick opens the next window */
}

/* Camp tick (task, inside rf_camp_watchdog_tick after the terminal check). Returns 1 when the
 * tick was a window open (the caller returns), 0 to run today's silent-tick logic. */
static uint8_t rf_win_camp_tick(void)
{
    uint32_t irq;

    if (!rf_bond_valid) {
        return 0u;                           /* the unbonded fresh-pair camp stays continuous (D5) */
    }
    if (!rf_win_mode) {
        if (rf_win_grace_ms > RF_WIN_CAMP_TICK_MS) {
            rf_win_grace_ms -= RF_WIN_CAMP_TICK_MS;
            return 0u;
        }
        rf_win_grace_ms = 0u; rf_win_mode = 1u; rfd_win_engages++;
    }
    irq = __risc_v_disable_irq();
    if (!rf_camp_is_terminal()) {
        rf_camp_wd_active = 0u;              /* the camp ended under us: self-disable, as the tick does */
        (void)__risc_v_enable_irq(irq);
        return 1u;
    }
    if (!rf_camp_wd_active) {
        (void)__risc_v_enable_irq(irq);
        return 1u;                           /* ownership already passed to a sink accept */
    }
    hal_event_cancel(RF_EVT_RX_RESTART);
    rf_start_rx();                           /* the camp's own arm: session AA, channel 8 */
    if (rf_win_fault_next) {                 /* rung 3: a deaf window; the next tick must recover */
        rf_win_fault_next = 0u; hal_rf_shut(); rfd_win_faults++;
    }
    rf_win_open = 1u; rf_win_phase_open = 0u; rf_win_accepted = 0u;
    rfd_win_opens++;
    hal_event_post_delayed(RF_EVT_RX_WIN_CLOSE, RF_WIN_MS_TO_TICKS(DONGLE_RX_WINDOW_MS));
    (void)__risc_v_enable_irq(irq);
    rf_arm_retry_if_failed();
    if (rf_camp_wd_active) {
        hal_timer_arm(HAL_TMR_SLOT_BOOT_WINDOW, RF_WIN_MS_TO_TICKS(DONGLE_RX_PERIOD_MS), rf_boot_window_cb);
    }
    return 1u;
}

/* True only when the radio is genuinely shut with nothing to serve: windowed mode,
 * no window open, and NO LIVE LINK. The connected state also has no window open
 * (its receiver is armed by the poll cycle, not by a window), so without the state
 * test this would report "radio off" between two 875 us polls and let a caller stop
 * the clocks across the grid. */
__HIGH_CODE
uint8_t RF_WinRadioOff(void)
{
    return (uint8_t)(rf_win_mode && !rf_win_open && !rf_win_accepted
                     && rf_state != RF_STATE_CONNECTED);
}

#if DONGLE_PM_HALT
void pm_halt_diag(uint32_t *halts, uint32_t *ticks, uint16_t *usb_wakes);   /* pm_ch592.c */
void pm_halt_diag2(uint32_t *abandons, uint32_t *reasons);                  /* pm_ch592.c */
#endif

static void rf_win_diag_fill(uint8_t *out)
{
    rfd_put32(&out[2],  rfd_win_opens);
    rfd_put32(&out[6],  rfd_win_closes);
    rfd_put32(&out[10], rfd_win_phase_opens);
    rfd_put32(&out[14], rfd_win_phase_misses);
    rfd_put32(&out[18], rfd_win_catches);
    rfd_put32(&out[22], rfd_win_locks);
    rfd_put32(&out[26], rfd_win_unlocks);
    rfd_put32(&out[30], rfd_win_engages);
    rfd_put16(&out[34], rf_win_link_rx);
    rfd_put16(&out[36], rf_win_phase_ms);
    rfd_put32(&out[38], rf_win_grace_ms);
    out[42] = (uint8_t)((rf_win_mode ? 1u : 0u) | (rf_win_open ? 2u : 0u)
                        | (rf_win_phase_open ? 4u : 0u) | (rf_win_locked ? 8u : 0u));
    out[43] = rf_win_misses;
    rfd_put32(&out[44], rfd_win_faults);
    out[48] = rfd_win_unsched_rx; out[49] = rfd_win_unsched_long;
    out[50] = rfd_win_unsched_late; out[51] = rfd_win_uncadenced;
#if DONGLE_PM_HALT
    {
        uint32_t h, tk, at, rw; uint16_t uw;
        pm_halt_diag(&h, &tk, &uw); pm_halt_diag2(&at, &rw);
        rfd_put32(&out[52], h);                    /* halts that returned */
        rfd_put32(&out[56], tk);                   /* RTC ticks actually halted */
        rfd_put16(&out[60], (uint16_t)((at > 0xFFFFu) ? 0xFFFFu : at));   /* abandoned at the last look */
        /* The page is full at 62 bytes; the abandon reasons and the backstop/USB counts ride
         * page 5's spare high nibble is taken, so they stay debugger-only for now. */
        (void)rw; (void)uw;
    }
#endif
}
#endif /* DONGLE_RX_WINDOW */

static void rf_enter_stock_reacquire(void)
{
    rfd_supervision_lapses++;
#if DONGLE_RX_WINDOW
    rf_win_on_lapse();
#endif
    rfd_reacq_entry_systick = hal_timing_systick_now();
#if !RF_TASK_EXECUTOR_TMOS
    if (rf_ch570_connected_rx_count == 0u) {
        rf_return_to_fresh_pair();
        return;
    }
#endif

#if RF_TASK_EXECUTOR_TMOS
    /* Codex full-batch review (+ 2-fix re-review): send the all-keys-up and LEAVE
     * CONNECTED under one IRQ mask. rf_send_keys_up_on_link_loss only fires while
     * rf_state==CONNECTED, and the connected RX sink (radio IRQ) forwards a
     * key-DOWN while CONNECTED — so without this, a late HID RX landing between the
     * keys-up here and the rf_state flip below would forward a key-down that is
     * then torn down with no key-up (stuck key). Setting rf_state out of CONNECTED
     * atomically with the keys-up closes that RF-ordering window.
     *
     * CH570 uses its established non-TMOS path below.
     * KNOWN RESIDUAL (Codex, NOT closed here): this closes the RF-state ordering
     * race, not the full host-delivery guarantee — a key-DOWN already consumed by
     * the host can leave a pending EP1 completion IRQ that NAKs the newly-stashed
     * keys-up after unmask; fully closing that needs USB endpoint-completion
     * ownership in the shared usb_device.c (a separate all-chip effort). The
     * RF-ordering race itself is very narrow (a supervision lapse means the
     * keyboard has gone silent, so an inbound key-DOWN at this instant is
     * contradictory). The redundant rf_state=IDLE at the camp setup below is
     * harmless. */
    uint32_t ku_irq = __risc_v_disable_irq();
    rf_send_keys_up_on_link_loss();
    rf_state = RF_STATE_IDLE;
    (void)__risc_v_enable_irq(ku_irq);
#else
    rf_send_keys_up_on_link_loss();
#endif

    hal_timer_cancel(HAL_TMR_SLOT_CONNECTED_POLL);
    hal_event_cancel(RF_EVT_POLL);
    hal_event_cancel(RF_EVT_POST_POLL_RX);
    hal_event_cancel(RF_EVT_SEND_PAIR_ACK);
    hal_event_cancel(RF_EVT_PAIR_PREP);
    rf_abort_pair_burst();

    rf_boot_window_active = 0;
    rf_pair_window_open = 0;
    rf_stock_first_supervision_armed = 0;

    /* Match the production shape: event 0x10 tears down to state 0, then
     * connection_setup enters state 1 and starts event-0x20 scanning. */
    rf_state = RF_STATE_IDLE;
    rf_access_addr = rf_bond_aa;
    rf_conn_interval = rf_active_conn_interval();
    rf_conn_timeout = rf_active_conn_timeout();
    rf_data_ch_idx = rf_proto_hop_seed(rf_pair_ack15[4]);
    rf_pair_prep_idx = rf_proto_pair_scan_seed(rf_pair_ack15[4]);
    rf_channel = rf_pair_channels[rf_pair_prep_idx];
    rf_supervision_ev10_active = 1;
    rfd_ev10_entries++;

    hal_rf_shut();
    rf_configure(rf_access_addr);

    rf_state = RF_STATE_PAIRING;
    hal_event_post(RF_EVT_PAIR_PREP);
    hal_timer_arm(HAL_TMR_SLOT_EV10_REKEY,
                  RF_SUPERVISION_STOCK_WATCHDOG_TMOS * HAL_TMOS_UNIT_TICKS,
                  rf_ev10_rekey_cb);
    
}

#ifdef RF_CH570_ARM_RETRY_TMOS
/* Old override name (pre-P1/P4-port). Renamed to RF_ARM_RETRY_TMOS; fail loudly
 * so a custom build using the old knob does not silently lose it. */
#error "RF_CH570_ARM_RETRY_TMOS was renamed to RF_ARM_RETRY_TMOS"
#endif
#ifndef RF_ARM_RETRY_TMOS
/* dongle_target.h (included first, unconditionally) MUST define this. Checked for
 * ALL executors (CH570 + CH59x) as of the P1/P4 port. */
#error "RF_ARM_RETRY_TMOS must be defined by the target header"
#endif
#if RF_ARM_RETRY_TMOS == 0
/* A 0 delay would make the failed-arm reschedule fire immediately and, on a
 * persistent arm failure, hot-spin RF_EVT_RX_RESTART — never let it apply. */
#error "RF_ARM_RETRY_TMOS must be > 0"
#endif
/* P4 deaf-camp guard (SHARED: CH570 polled + CH59x TMOS). Call immediately after
 * arming RF_Rx in a terminal camp whose only re-arm driver would otherwise be a
 * radio RX timeout (the give-up reacquire camp, the closed boot window, the
 * connected self-heal loop). If that arm FAILED the radio never started, so
 * nothing ever re-drives the camp and it is silently deaf forever — worse on
 * CH59x, whose basic-mode RF_Rx has NO hardware timeout at all (hal_rf_ch592.c),
 * so the guard is the SOLE backstop there. Schedule an independent
 * RF_EVT_RX_RESTART so the re-arm loop restarts; the restart re-arms and, if it
 * fails too, re-schedules — the loop self-sustains until an arm succeeds, then
 * the normal RX-completion re-drive resumes. TASK-context only: the arm
 * functions also run from the radio IRQ sink (RF_CONNECTED_RX_REARM), which must
 * NOT schedule here — that path has the supervision watchdog as its backstop. */
static void rf_arm_retry_if_failed(void)
{
    if (rf_last_arm_status != 0u) {
        /* RESIDUAL (accepted, same as CH570): hal_event_post_delayed is void, so
         * a failed TMOS timer-node allocation is not detected here — the camp
         * would stay deaf and this counter would plateau. Every terminal camp
         * that relies on this guard CANCELS all four timer slots + its events
         * first, so the TMOS timer pool has free nodes when this runs; the bench
         * fault-injection confirms the reschedule actually fires. */
        hal_event_post_delayed(RF_EVT_RX_RESTART,
                               RF_ARM_RETRY_TMOS * HAL_TMOS_UNIT_TICKS);
        rfd_arm_retry_scheduled++;
    }
}

static uint32_t rf_camp_wd_events(void)
{
    hal_rf_diag_t h;
    hal_rf_diag_snapshot(&h);
    return h.rx_done + h.rx_crcerr + h.rx_timeout;
}

/* The exact terminal camp the watchdog (and the 0x94 ladder) may act on:
 * PAIRING, no EV10 scan, no boot window, no burst, not quiescing. */
static uint8_t rf_camp_is_terminal(void)
{
    return (uint8_t)(rf_state == RF_STATE_PAIRING && !rf_supervision_ev10_active
                     && !rf_boot_window_active && !rf_inject_burst_active
                     && !rf_quiesced);
}

/* Task context, at every terminal-camp entry: start the liveness tick. */
static void rf_camp_watchdog_arm(void)
{
    rf_camp_wd_seen   = rf_camp_wd_events();
    rf_camp_wd_silent = 0u;
    rf_camp_wd_active = 1u;
    hal_timer_arm(HAL_TMR_SLOT_BOOT_WINDOW, RF_CAMP_WD_TICKS_TSYS, rf_boot_window_cb);
}

/* Task context, one tick: RF_EVT_BOOT_WINDOW with the window closed. */
static void rf_camp_watchdog_tick(void)
{
    uint32_t seen, irq;

    if (!rf_camp_is_terminal()) {
        rf_camp_wd_active = 0u;           /* the camp ended: self-disable */
        return;
    }
#if DONGLE_RX_WINDOW
    if (rf_win_camp_tick()) {
        return;
    }
#endif
    seen = rf_camp_wd_events();
    if (seen != rf_camp_wd_seen) {
        rf_camp_wd_seen   = seen;         /* alive: leave the radio alone */
        rf_camp_wd_silent = 0u;
    } else {
        if (rf_camp_wd_silent < 0xFFu) {
            rf_camp_wd_silent++;
        }
        /* Predicate and action under one IRQ mask (the 0x94 ladder's model):
         * between an unmasked check and the re-arm the radio sink can accept
         * a beacon and start a pair-ACK burst this must not tear through. */
        irq = __risc_v_disable_irq();
        if (!rf_camp_is_terminal()) {
            (void)__risc_v_enable_irq(irq);
            rf_camp_wd_active = 0u;
            return;
        }
        hal_event_cancel(RF_EVT_RX_RESTART);   /* a stale restart must not race us */
#if !RF_TASK_EXECUTOR_TMOS
        if (rf_camp_wd_silent >= 2u) {     /* the timeout loop is dead: re-init */
            hal_rf_shut();
            hal_rf_init();
            rfd_camp_wd_reinits++;
        }
#endif
        rf_start_rx();
        rfd_camp_wd_rearms++;
        (void)__risc_v_enable_irq(irq);
        rf_arm_retry_if_failed();
    }
    /* Re-arm only while still the slot's owner: a beacon accepted in the
     * radio sink meanwhile cancelled the slot and cleared the flag, and the
     * trailing arm must not bring it back (Copilot). The window between this
     * read and the arm is a few instructions; a sink accept inside it costs
     * one expiry whose tick self-disables. */
    if (rf_camp_wd_active) {
        hal_timer_arm(HAL_TMR_SLOT_BOOT_WINDOW, RF_CAMP_WD_TICKS_TSYS, rf_boot_window_cb);
    }
}

/* P1' pair-ACK TX guard. Call with the hal_rf_start_tx() status right after a
 * pair-ACK burst TX. On CH570 a SYNCHRONOUS StartTx refusal (RFIP_StartTx returns
 * nonzero) raises no TX_FINISH, so the burst chain never advances and RX is never
 * re-armed — a deaf strand with no recovery timer (the TX-side twin of the P4
 * RX-arm gap; note CH570 never raises TX_FAIL, so the shared TX_MODE_TX_FAIL path
 * is unreachable here). Recover through the proven unconfirmed-pair boot-window
 * relisten, which camps on rf_bond_aa (== the advertised session AA on a fresh
 * dongle) AND alternates onto the pair AA; the LEN-10 accept gate then re-hears
 * the keyboard on either AA — a fresh dongle via its !rf_bond_valid clause, a
 * bonded dongle accepting a new keyboard via the known-peer MAC match. Returns
 * nonzero if it recovered (caller must not keep chaining the burst).
 * RESIDUAL (not covered): a StartTx that returns 0 then silently never raises
 * TX_FINISH would still stall the burst; unobserved on CH570 (the bench repro is
 * the nonzero-return kind) and would need a burst watchdog timer to close. */
static uint8_t rf_pair_tx_recover_if_failed(uint8_t status)
{
    if (status == 0u) {
        return 0u;
    }
    rf_return_to_fresh_pair();   /* aborts the burst + boot-window relisten */
    return 1u;
}

static void rf_stock_reacquire_giveup(void)
{
    rfd_ev10_giveups++;
    rfd_giveup_systick = hal_timing_systick_now();
    rf_supervision_ev10_active = 0;
    rf_stock_first_supervision_armed = 0;
    rf_last_conn_rx_tsys = 0;
    rf_boot_window_active = 0;
    rf_pair_window_open   = 0;

    /* FULL timer + event teardown (v0.95 hardening, bench 2026-07-05): the
     * failed EV10 cycle can leave CONNECTED_POLL / EV10_REKEY armed (the
     * grid-align promote sites re-arm them mid-cycle), and any stale dispatch
     * leaking into the camp races the reconnect-accept burst this camp exists
     * to serve. Tear down every slot and event the connected machinery owns
     * so the camp is exactly as quiescent as the post-boot-window state.
     * Validated: keyboard killed mid-link -> timeout/reacquire/giveup ->
     * keyboard's autonomous boot reconnect links against this camp in ~0.2 s. */
    hal_timer_cancel(HAL_TMR_SLOT_CONNECTED_POLL);
    hal_timer_cancel(HAL_TMR_SLOT_PAIR_ACK);
    hal_timer_cancel(HAL_TMR_SLOT_EV10_REKEY);
    hal_timer_cancel(HAL_TMR_SLOT_BOOT_WINDOW);
    rf_camp_wd_active = 0u;   /* the slot is the camp watchdog's tick too */
    hal_event_cancel(RF_EVT_PAIR_PREP);
#if DONGLE_RX_WINDOW
    hal_event_cancel(RF_EVT_RX_WIN_CLOSE);
    hal_event_cancel(RF_EVT_RX_WIN_PHASE);
    rf_win_open = 0u; rf_win_phase_open = 0u; rf_win_accepted = 0u;
    if (rf_win_locked) { rf_win_locked = 0u; rfd_win_unlocks++; }   /* the probes stopped: no lock to keep */
    rf_win_sched_runs = 0u;
#endif
    hal_event_cancel(RF_EVT_SEND_PAIR_ACK);
    hal_event_cancel(RF_EVT_POLL);
    hal_event_cancel(RF_EVT_POST_POLL_RX);
    rf_abort_pair_burst();
#if RF_CONFIRM_BEFORE_PERSIST
    /* Codex fix re-review: a WAIT_REARM here means the peer HAD confirmed the
     * session (a valid connected RX was seen) but the post-confirm rearm never
     * succeeded and reacquire has now exhausted. The pair is genuine, so make it
     * durable before giving up (matches the confirm-timeout WAIT_REARM branch);
     * otherwise a confirmed bond is silently lost if this races ahead of the
     * confirm deadline (e.g. a failed RF_EVT_CONFIRM_TIMEOUT allocation). */
    /* Codex 2-fix re-review (blocking): claim the confirm state under an IRQ mask
     * (the confirm-timeout handler's model). Giveup runs in task context but a late
     * EV10 TX_FINISH can promote back to CONNECTED just before this, and the radio
     * IRQ sink can advance WAIT_RX->WAIT_REARM (and forward HID) between an unmasked
     * read and our action -> wrong routing / lost persist / HID-without-keys-up.
     * Snapshot + clear the confirm state and leave CONNECTED atomically, then act. */
    uint32_t gv_irq = __risc_v_disable_irq();
    uint8_t gv_confirm = rf_confirm_state;
    rf_confirm_state = RF_CONFIRM_STATE_NONE;   /* N11: no tentative pair survives giveup */
    if (rf_state == RF_STATE_CONNECTED) {
        /* a late EV10 promote restored CONNECTED; leave it inside the mask so the
         * sink can't forward a key-DOWN or advance the confirm state after here. */
        rf_state = RF_STATE_PAIRING;
    }
#if RF_TASK_EXECUTOR_TMOS
    rf_burst_txfail_fallback = 0u;
#endif
    (void)__risc_v_enable_irq(gv_irq);
    if (gv_confirm == RF_CONFIRM_STATE_WAIT_REARM) {
        rf_arm_bond_persist();
    } else if (gv_confirm == RF_CONFIRM_STATE_WAIT_RX) {
        /* Codex full-batch review (#3, low): an UNCONFIRMED fresh pair reached
         * giveup. Normally RF_EVT_CONFIRM_TIMEOUT routes an unconfirmed pair to the
         * dual-AA fresh-pair fallback, but if that delayed post failed to allocate
         * there is no deadline, so reacquire exhaustion lands here instead. The
         * keyboard may still be pair-broadcasting on the PAIR AA, which the
         * reconnect-only camp below cannot hear. Return to the dual-AA boot-window
         * relisten (rf_return_to_fresh_pair re-camps BOTH AAs) instead of stranding
         * on the session-AA reconnect camp. */
        rf_return_to_fresh_pair();
        return;
    }
    hal_event_cancel(RF_EVT_CONFIRM_TIMEOUT);
#endif

    rf_state = RF_STATE_PAIRING;
    /* Camp EXACTLY like the closed boot window (RF_EVT_BOOT_WINDOW terminal
     * state, bench-proven for months): session AA + channel 8, reconnect-only.
     * rf_bond_aa — NOT rf_bond_default_aa: the default is the PAIR AA until a
     * bond is loaded/persisted, and this path only runs after a connection
     * existed, where rf_bond_aa is the live session AA the keyboard will
     * reconnect on. (Like the closed boot window, pairing a NEW keyboard
     * from this camp needs a dongle replug.) */
    rf_access_addr = rf_bond_aa;
    rf_channel = RF_PROTO_RECONNECT_CAMP_CHANNEL;
    rf_start_rx();
    rf_arm_retry_if_failed();   /* P4: don't strand deaf on a failed arm */
    rf_camp_watchdog_arm();     /* and never on a lost completion or a deaf PHY */
}

/* ---------- RF status callback (runs in interrupt context) ---------- */






/* PHY-event sink (P2.4): registered with the seam via hal_rf_set_event_cb at
 * RF_TaskInit. The CH592 vendor callback (RF_2G4StatusCallBack, now a thin
 * extractor in hal_rf_ch592.c) maps (sta, rsr) onto hal_rf_event_t and calls
 * here -- one event per invocation. CONTEXT: the CH59x BLE controller runs this
 * sink as an IRQ-tail DEFERRED callback (TMOS_SysRegister/tmosSign ECALL
 * trampoline in ble_task_scheduler.S), NOT a raw BB/LLE ISR -- but it can still
 * PREEMPT RF_ProcessEvent before the interrupted foreground/TMOS work resumes,
 * so state shared with the task (e.g. the hal_timing TMR0 arm/cancel latch) must
 * be guarded; it is NOT cooperatively serialized. The legacy body below
 * is preserved VERBATIM (it is heavily bench-validated); the (sta, rsr) pair
 * it branches on is re-synthesized from the event. */
/* IAP 0x92: name the gate a LEN-10 fell through (mirrors the accept condition
 * in the sink; evaluated only on the reject path, counters only). */
__HIGH_CODE
static uint8_t rf_diag_len10_reject_reason(const uint8_t *rxBuf)
{
    if (rf_bond_tombstone) {
        return RFD_L10_REJ_TOMBSTONE;
    }
    if (rf_bond_valid && !rf_pair_window_open) {
        return RFD_L10_REJ_LOCKED;      /* bonded lockout: window closed and the
                                         * known-peer disjunct did not match */
    }
    if (!rf_accept_peer_mac(&rxBuf[2])) {
        return RFD_L10_REJ_BAD_MAC;
    }
    if (rf_rssi < RF_PAIR_MIN_RSSI) {
        return RFD_L10_REJ_RSSI;
    }
    return RFD_L10_REJ_OTHER;
}

__HIGH_CODE
static void rf_phy_event_sink(hal_rf_event_t ev, const uint8_t *rx, uint8_t rxlen)
{
    uint8_t *rxBuf = (uint8_t *)rx;
    uint8_t sta, rsr;

    (void)rxlen;
    /* Quiesce gate: an IRQ tail already in flight when hal_rf_shut() ran
     * must not re-arm RX/TX out of the shut radio. */
    if (rf_quiesced) {
        return;
    }
    switch (ev) {
    case HAL_RF_EV_RX_DONE:   sta = RX_MODE_RX_DATA;   rsr = 0; break;
    case HAL_RF_EV_RX_CRCERR: sta = RX_MODE_RX_DATA;   rsr = 1; break;
    case HAL_RF_EV_TX_DONE:   sta = TX_MODE_TX_FINISH; rsr = 0; break;
    case HAL_RF_EV_TX_FAIL:   sta = TX_MODE_TX_FAIL;   rsr = 0; break;
    case HAL_RF_EV_RX_TIMEOUT:
        /* The extractor maps unknown vendor sta here (codex P2.4 #1): give
         * the preserved body a sta no case matches so it falls into its
         * switch default -- the legacy defensive RX_RESTART. */
        sta = 0xFFu; rsr = 0; break;
    default:
        return;
    }
    /* The stock control-byte feedback (rf_proto_ctrl_update) used to run
     * HERE, on every good RX before the state switch. That acked frames this
     * task never admitted: a LEN-10 that the not-CONNECTED consumer below
     * swallowed as a beacon (or rejected) still flipped our poll bit, and the
     * keyboard's ack-retired FIFO released a report we never dispatched.
     * Bench 2026-09-13: first key after a dongle reset, keyboard
     * ll_hid_tx_done_down advanced, rfd_hid_rx unchanged, no retransmit. The
     * feedback now lives in the CONNECTED handler, applied only to a frame
     * this session admits (a LEN-1 keepalive or a classified HID report), so
     * an ack means "admitted by the RF task" -- it precedes the optional
     * forwarding callback; the EP1 queue's counters cover the USB hop. */
    switch (sta) {
    case RX_MODE_RX_DATA:
        if (rsr != 0) {
            /* CRC error or type mismatch - restart RX */
            hal_event_post(RF_EVT_RX_RESTART);
            break;
        }

        rf_rssi = (int8_t)rxBuf[0];

        /* Gate the pair/listener decoder block on NOT-CONNECTED.
         * Once we've reached state==CONNECTED, this path can consume packets
         * before the normal CONNECTED-state RX handler runs. Skip it so
         * control falls through to the `rf_state == RF_STATE_CONNECTED`
         * handler around line 1401. */
        if (rf_state != RF_STATE_CONNECTED
            && !rf_supervision_ev10_active
        ) {
            /* LEN=10 keyboard pair broadcast on the pair-broadcast
             * access address. Layout per PROTOCOL.md:
             *   [0..5]  keyboard MAC (6 bytes)
             *   [6..7]  conn_interval (u16 LE)
             *   [8..9]  conn_timeout  (u16 LE)
             * NOTE: this catches LEN=10 packets BEFORE the HID-report
             * decoder below while not CONNECTED. On the session access
             * address the keyboard's HID reports also have LEN=10 with
             * rxBuf[3]==0xA1; bonded lockout below prevents treating normal
             * HID as a known-peer reconnect unless its first 6 payload bytes
             * exactly match the peer MAC. */
            if (rxBuf[1] == 10
                && !rf_supervision_ev10_active
                /* CODEREVIEW N06: after a host BondClear, accept no new pair (nor
                 * a reconnect of the just-cleared bond) until the next reset --
                 * BondClear is a completed transaction, so nothing repopulates a
                 * record the host just erased. */
                && !rf_bond_tombstone
                /* Accept a known-peer reconnect unconditionally (its LEN=10
                 * broadcast on the bonded AA must reconnect at any range), but
                 * gate a fresh pair, or a boot-window accept of a DIFFERENT
                 * keyboard, on signal strength: an unprovisioned dongle must
                 * not auto-pair to a distant/unintended keyboard that happens
                 * to be broadcasting in a dense test/user environment. The
                 * bonded lockout (reject a different keyboard outside the boot
                 * window) is preserved by the (!rf_bond_valid||window) guard. */
                /* CODEREVIEW V2 (site 1): the known-peer disjunct must not
                 * match a zero/broadcast peer — a provisioned zero-peer
                 * (learn-mode) record left rf_peer_mac all-zero, and a
                 * crafted all-zero LEN-10 then matched 6-of-6 and was
                 * accepted unconditionally. A real keyboard's MAC is nonzero,
                 * so learn-mode records take the gated accept path below. */
                && ((rf_bond_valid && rf_accept_peer_mac(rf_peer_mac)
                     && tmos_memcmp(rf_peer_mac, &rxBuf[2], 6))
                    || ((!rf_bond_valid || rf_pair_window_open)
                        && rf_rssi >= RF_PAIR_MIN_RSSI
                        /* Reject an all-zero MAC on the accept-of-new path
                         * (V2, v0.96 review): a real keyboard always
                         * broadcasts its 6-byte non-zero MAC, so this only
                         * drops crafted/garbage LEN-10 frames. Load-bearing on
                         * CH570, whose RSSI byte is a constant 0xFF (the
                         * proximity gate is inert), where an accepted zero-MAC
                         * frame would persist a zero-peer bond that then
                         * open-reconnects to any zero-MAC frame. */
                        && rf_accept_peer_mac(&rxBuf[2])))
            ) {
                /* Learn the keyboard (peer) MAC from the pair broadcast so a
                 * completed pair can be persisted to the bond record. */
#if !RF_TASK_EXECUTOR_TMOS
                /* Persist a boot-window peer change (review D6) — see the
                 * helper. Must run BEFORE the memcpy overwrites rf_peer_mac. */
                rf_relatch_bond_on_peer_change(&rxBuf[2]);
#endif
#if RF_CONFIRM_BEFORE_PERSIST
                /* CODEREVIEW N11: classify this accept as a KNOWN-DURABLE reconnect
                 * vs a fresh/tentative pair, BEFORE rf_peer_mac is overwritten. A
                 * reconnect is durable ONLY if the bond is valid AND already
                 * verified in DataFlash AND we are camped on that bond's session AA
                 * AND the broadcaster MAC matches the stored peer. Everything else
                 * is fresh: crucially, a RETRY after a timed-out fresh pair still
                 * has rf_bond_persisted == 0, so it stays fresh and cannot persist
                 * without a fresh confirmation.
                 *
                 * KNOWN LIMITATION -- N11 is PARTIAL for bond-replacing re-pairs
                 * (Codex impl-review; OWNER-ACCEPTED WONTFIX 2026-07-13): such a
                 * re-pair reuses the loaded session AA (advertised in the pair-ACK),
                 * which the OLD keyboard also knows. If the new keyboard misses every
                 * ACK yet the old keyboard is still powered and polling that AA, the
                 * old keyboard's LEN-1 satisfies the confirm for the NEW candidate ->
                 * a dead bond (new MAC + old AA) is persisted; the user recovers by
                 * simply restarting pairing. This is narrower than pre-N11 (which
                 * persisted an unconfirmed re-pair UNCONDITIONALLY) and requires two
                 * keyboards both ACTIVE during a deliberate re-pair -- it cannot
                 * occur in single-keyboard use, nor in steady-state reconnect (a
                 * reconnect never rewrites the bond; only the pairing moment does).
                 * A full fix was designed (advertise a freshly generated candidate
                 * AA for a bond-replacing re-pair so only the new keyboard can
                 * confirm, with a RAM shadow + rollback) but deemed not worth the
                 * state-machine complexity for this narrow, user-recoverable case. */
                {
                    uint8_t peer_mac_eq =
                        tmos_memcmp(rf_peer_mac, &rxBuf[2], 6) ? 1u : 0u;
                    uint8_t known_durable = rf_bond_valid && rf_bond_persisted
                                          && rf_access_addr == rf_bond_aa
                                          && peer_mac_eq;
                    rf_pair_is_fresh = known_durable ? 0u : 1u;
                    if (rf_pair_is_fresh) {
                        rf_bond_persisted = 0;  /* tuple not the verified DataFlash one */
                    }
                }
                rfd_len10_seen++;
                if (rf_pair_is_fresh) {
                    rfd_len10_accept_fresh++;
                    rfd_len10_last_disp = RFD_L10_ACCEPT_FRESH;
                } else {
                    rfd_len10_accept_known++;
                    rfd_len10_last_disp = RFD_L10_ACCEPT_KNOWN;
                }
#endif
                tmos_memcpy(rf_peer_mac, &rxBuf[2], 6);
                /* A new pair is now in progress (this only runs for a fresh
                 * dongle, or a bonded one inside its boot window — see the
                 * lockout guard above). Close the boot window so its AA
                 * alternation can't flip rf_access_addr out from under the
                 * pair-ACK handshake we're about to start. Clearing the flag
                 * makes the next RF_EVT_BOOT_WINDOW tick a no-op; the
                 * tmos_stop_task drops the already-scheduled one too. */
                rf_boot_window_active = 0;
                rf_pair_window_open   = 0;
                hal_timer_cancel(HAL_TMR_SLOT_BOOT_WINDOW);
                rf_camp_wd_active = 0u;   /* the slot is the camp watchdog's tick too */
                /* Arm the burst state machine — the IRQ-side TX_FINISH
                 * for this first TX will then chain RF_EVT_TX_PAIR_15B
                 * to fire 5 more 15-byte TXes on session AA across the
                 * data-channel LUT. */
                rf_inject_burst_active = 1;
                rf_inject_burst_idx    = 0;
                /* Trigger the 15-byte pair-ACK TX from task context.
                 * Don't restart RX yet — the TX path will re-arm RX
                 * after TX_FINISH so we keep watching for the keyboard
                 * to either (a) stop broadcasting (success) or (b)
                 * keep going (need to re-TX). */
#if !RF_TASK_EXECUTOR_TMOS && RF_CH570_PAIR_ACK_PRE_TX_TMOS
                /* Give the keyboard its turnaround window before we answer.
                 * NOTE: hal_event_post_delayed() has two slots and degrades to
                 * an IMMEDIATE post if both are taken -- which would silently
                 * restore the broken behaviour. The other consumers (pair-prep
                 * cadence, burst gap) do not overlap this instant. */
                hal_event_post_delayed(RF_EVT_TX_PAIR_15,
                    RF_CH570_PAIR_ACK_PRE_TX_TMOS * HAL_TMOS_UNIT_TICKS);
#else
                hal_event_post(RF_EVT_TX_PAIR_15);
#endif
                rfd_pair_ack_posted++;
                rfd_ack_accept_systick = (uint32_t)SysTick->CNT;
                break;
            }

            /* IAP 0x92: a LEN-10 that fell through the accept gate above. */
            if (rxBuf[1] == 10) {
                rfd_len10_seen++;
                rfd_len10_rejected++;
                rfd_len10_last_disp = rf_diag_len10_reject_reason(rxBuf);
            }
            /* Ignore any non-pair packet while listening for a connection. */
            hal_event_post(RF_EVT_RX_RESTART);
            break;
        }


        if (rf_state == RF_STATE_CONNECTED) {
            uint8_t len = rxBuf[1];
            uint32_t rx_now = hal_now();   /* P3a: supervision lapse is
                                            * measured on Tsys (2^32 modular;
                                            * stamps refresh every RX, reads
                                            * within the 10 s deadline) */
            rf_last_conn_rx_tsys = rx_now;
#if DONGLE_RX_WINDOW
            if (rf_win_link_rx != 0xFFFFu) { rf_win_link_rx++; }
#endif

#if !RF_TASK_EXECUTOR_TMOS
            rf_ch570_connected_rx_count++;
#endif

            /* A LEN-10 from the known peer showing up in CONNECTED means our
             * previous session ended on the keyboard's side (it is
             * re-broadcasting). The supervision/EV10 machinery handles the
             * recovery. */


            /* Dispatch HID data if callback registered and payload present.
             * On-wire layout (validated against sniff-mode decoder at the
             * top of this file): rxBuf[0]=RSSI, rxBuf[1]=LEN, rxBuf[2]=ctrl,
             * rxBuf[3]=0xA1 (HID tag), rxBuf[4..] = HID report. For LEN=10
             * that's an 8-byte boot-keyboard report starting at rxBuf[4].
             * Gate on the 0xA1 tag so non-HID traffic (e.g. LEN=3 LED
             * relay at rxBuf[3]=0xA1, LEN=6 event-0x20 TXes, LEN=1 polls)
             * doesn't get misclassified as a keyboard report. */
            {
                uint8_t hid_tag =
                    rf_proto_hid_report_tag_for_peer(rxBuf, len, rf_peer_mac);
#if DONGLE_BENCH_DROP_FIRST_HID
                /* Bench fault injection: swallow the first non-zero boot-keyboard
                 * report after each promote before the reception counters, the
                 * feedback and the forwarding callback, so it is neither counted
                 * nor acked nor forwarded (it still refreshes liveness and
                 * supervision like any connected RX). Whether the keyboard's
                 * ack-retired FIFO then loses that report or retransmits it is
                 * exactly what the control-byte feedback placement decides. */
                if (rf_bench_drop_armed && hid_tag == RF_PROTO_HID_TAG
                    && (rxBuf[4]|rxBuf[5]|rxBuf[6]|rxBuf[7]|rxBuf[8]|rxBuf[9]|rxBuf[10]|rxBuf[11])) {
                    rf_bench_drop_armed = 0u;
                    rf_bench_drops++;
                    hid_tag = 0u;
                }
#endif
                /* Control-byte feedback (stock PROTOCOL.md formula, bit 1 =
                 * the keyboard's fresh-packet indicator; we flip bit 0 when it
                 * changes) -- ONLY for a frame this session admits, so the
                 * keyboard retires a report exactly when the RF task accepts
                 * it (the forwarding callback follows). A frame the injection
                 * above swallowed, or one the classifier rejects, must not be
                 * acked. */
                if (len == 1u || hid_tag != 0u) {
                    rf_poll_buf[0] = rf_proto_ctrl_update(rf_poll_buf[0], rxBuf[2]);
                }
#if DONGLE_DELIVERY_COUNTERS
                if (hid_tag) {   /* pre-forward RF reception of a peer HID report */
                    rfd_hid_rx++;
                    /* Boot keyboard only: the classifier returns RF_PROTO_HID_TAG solely
                     * for an exact LEN-10 frame (it rejects a short 0xA1 precisely so a
                     * sink cannot read past the body), so the tag alone makes the 8-byte
                     * read in bounds. Consumer 0xA3 and mouse 0xA8 have shorter bodies and
                     * route to EP3/EP2, not the EP1 path this is compared against. */
                    if (hid_tag == RF_PROTO_HID_TAG
                        && (rxBuf[4]|rxBuf[5]|rxBuf[6]|rxBuf[7]|rxBuf[8]|rxBuf[9]|rxBuf[10]|rxBuf[11])) {
                        rfd_hid_rx_down++;
                    }
                }
#endif
                if (hid_tag && rf_hid_callback) {
                    rf_hid_callback(hid_tag, &rxBuf[4], len - 2);
                }
#if RF_CONFIRM_BEFORE_PERSIST
                /* CODEREVIEW N11: a valid connected RX from the peer confirms it
                 * accepted the tentative fresh-pair session. A LEN-1 poll ack OR a
                 * validated HID tag (0xA1, peer-matched — hid_tag != 0) both
                 * count; LEN-3 LED relays, LEN-6, and noise do not (that is why
                 * confirmation cannot be spoofed by non-peer traffic). Latch only;
                 * the durable write is armed later, after a successful RX re-arm. */
                if (rf_confirm_state == RF_CONFIRM_STATE_WAIT_RX
                    && (len == 1u || hid_tag != 0u)) {
                    rf_confirm_state = RF_CONFIRM_STATE_WAIT_REARM;
                }
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
