openkeyboard-org/OpenDongle/firmware/ch592/src/hal_rf_ch592.c

/*
 * OpenKeyboard.org OpenDongle -- CH592 RF PHY HAL.
 * Copyright 2026 Eric Molitor (EMulator)
 * SPDX-License-Identifier: Apache-2.0
 *
 * Implements hal_rf.h over the LIBCH59xBLE radio (RF_Config / RF_SetChannel /
 * RF_Rx / RF_Tx / RF_Shut). This is the PHY seam: rf_task drives the radio
 * through hal_rf_*, and the vendor status callback here is reduced to pure
 * PHY-event extraction -- it maps the (sta, rsr) pair onto the chip-agnostic
 * hal_rf_event_t set and forwards one event per invocation to the
 * rf_task-registered sink (CH59x sta is a single enumerated state, never a
 * bitmask, so one callback == one event). All protocol/FSM logic stays in
 * rf_task.c.
 *
 * CH59x mapping quirks (vs the CH570 RFIP impl):
 *  - The access address and CRC live in RF_Config (hal_rf_configure);
 *    start_tx's access_addr argument is accepted for contract symmetry but
 *    the radio transmits with the configured AA.
 *  - Channel is persistent radio state set by RF_SetChannel; the
 *    HAL_RF_CHANNEL_CURRENT sentinel skips the retune, preserving the stock
 *    no-channel-set shapes (pair-ACK TX inherits the pair-prep channel;
 *    post-poll RX re-arms untouched).
 *  - RF_Rx has no hardware timeout in this basic-mode usage; the `timeout`
 *    argument is ignored (link supervision is TMOS-timer based).
 *  - RF_Rx's (txBuf, txLen) prime pair is passed through verbatim by
 *    hal_rf_start_rx_primed for stock-shape faithfulness.
 */
#include "CONFIG.h"
#include "hal_rf_ch592.h"

/* Mirrors the rf_task.c values exactly (PROTOCOL.md RF PHY parameters). */
#define HAL_RF_CH592_CRC_INIT  0x555555
#define HAL_RF_CH592_LLE_MODE  (LLE_MODE_BASIC | LLE_WHITENING_ON | LLE_MODE_PHY_2M)

static hal_rf_event_cb_t rf_event_cb;

/* Last RX frame base handed to the status callback. The BLE library owns the
 * buffer; the pointer is stable across a session in practice (hal_rf_rx_buf
 * contract: telemetry/decoding only). */
static const uint8_t *volatile rf_last_rx_frame;

void RF_2G4StatusCallBack(uint8_t sta, uint8_t rsr, uint8_t *rxBuf);

/* IAP 0x92 page 1 PHY counters, the same contract the CH570 executor fills:
 * arms and their status, and the vendor events as forwarded. The
 * receive-side pair (tx_done = polls sent, rx_done = replies received) is
 * the reply-rate oracle the power work needed: on this port a missed poll
 * reply raises no event at all (the next poll's shut aborts the RX), so it
 * shows only as rx_done falling behind tx_done. The event counters are
 * written by the callback only (one context); the arm and shut counters are
 * reached from the task AND from the IRQ-tail sink, so those increments are
 * single-instruction AMOs (amoadd.w) rather than load/add/store, which the
 * tail could split (codex review). */
#define RF_DIAG_INC(field)  ((void)__atomic_fetch_add(&rf_diag.field, 1u, __ATOMIC_RELAXED))
static hal_rf_diag_t rf_diag = { .last_rx_rc = 0xFFu, .last_tx_rc = 0xFFu, .last_shut_rc = 0xFFu };

void hal_rf_init(void)
{
    RF_RoleInit();
}

void hal_rf_set_event_cb(hal_rf_event_cb_t cb)
{
    rf_event_cb = cb;
}

const uint8_t *hal_rf_rx_buf(void)
{
    return rf_last_rx_frame;
}

void hal_rf_configure(uint32_t access_addr)
{
    rfConfig_t cfg;

    tmos_memset(&cfg, 0, sizeof(cfg));
    cfg.LLEMode       = HAL_RF_CH592_LLE_MODE;
    cfg.Channel       = 0;    /* RF_SetChannel selects the live channel later. */
    cfg.accessAddress = access_addr;
    cfg.CRCInit       = HAL_RF_CH592_CRC_INIT;
    cfg.rfStatusCB    = RF_2G4StatusCallBack;
    (void)RF_Config(&cfg);
}

void hal_rf_set_channel(uint8_t channel)
{
    RF_SetChannel(channel);
}

__HIGH_CODE
uint8_t hal_rf_start_rx(uint8_t channel, uint16_t timeout)
{
    uint8_t rc;
    (void)timeout;   /* no hardware RX timeout in basic mode; TMOS supervises */
    if (channel != HAL_RF_CHANNEL_CURRENT) {
        RF_SetChannel(channel);
    }
    rc = RF_Rx(NULL, 0, 0xFF, 0xFF);
    RF_DIAG_INC(rx_arm_attempts);
    rf_diag.last_rx_rc = rc;
    if (rc != 0u) RF_DIAG_INC(rx_arm_fail); else rf_diag.rx_armed = 1u;
    return rc;
}

__HIGH_CODE
uint8_t hal_rf_start_rx_primed(uint8_t channel, uint16_t timeout,
                               const uint8_t *prime_buf, uint8_t prime_len)
{
    uint8_t rc;
    (void)timeout;
    if (channel != HAL_RF_CHANNEL_CURRENT) {
        RF_SetChannel(channel);
    }
    rc = RF_Rx((uint8_t *)prime_buf, prime_len, 0xFF, 0xFF);
    RF_DIAG_INC(rx_arm_attempts);
    rf_diag.last_rx_rc = rc;
    if (rc != 0u) RF_DIAG_INC(rx_arm_fail); else rf_diag.rx_armed = 1u;
    return rc;
}

__HIGH_CODE
uint8_t hal_rf_start_tx(uint8_t channel, uint32_t access_addr,
                        const uint8_t *buf, uint8_t len)
{
    uint8_t rc;
    (void)access_addr;   /* AA comes from RF_Config (hal_rf_configure) */
    if (channel != HAL_RF_CHANNEL_CURRENT) {
        RF_SetChannel(channel);
    }
    rc = RF_Tx((uint8_t *)buf, len, 0xFF, 0xFF);
    RF_DIAG_INC(tx_start);
    rf_diag.rx_armed = 0u;          /* a TX start ends any armed RX (hal_rf.h contract) */
    rf_diag.last_tx_rc = rc;
    if (rc != 0u) RF_DIAG_INC(tx_fail);
    return rc;
}

void hal_rf_shut(void)
{
    RF_DIAG_INC(shut_calls);
    rf_diag.rx_armed = 0u;
    rf_diag.last_shut_rc = RF_Shut();
}

/*
 * Vendor status callback. CONTEXT: the BLE controller invokes this as an
 * IRQ-tail DEFERRED callback (TMOS_SysRegister/tmosSign trampoline), not a raw
 * BB/LLE ISR; it can preempt the foreground/TMOS task. Pure PHY-event extraction:
 * (sta, rsr) -> one hal_rf_event_t per invocation. rsr (bit0 CRC, bit1 type
 * match) collapses to the RX_DONE/RX_CRCERR split.
 */
__HIGH_CODE
void RF_2G4StatusCallBack(uint8_t sta, uint8_t rsr, uint8_t *rxBuf)
{
    hal_rf_event_t ev;
    uint8_t len = 0u;

    if (rxBuf) {
        rf_last_rx_frame = rxBuf;
    }
    /* Diagnostic accounting first, for every event, whether or not a sink
     * is registered (a status event during callback setup or teardown must
     * still count and still end the armed-RX latch: CodeRabbit review). */
    switch (sta) {
    case RX_MODE_RX_DATA:
        rf_diag.rx_armed = 0u;
        if (rsr == 0) {
            rf_diag.rx_done++;
            ev = HAL_RF_EV_RX_DONE;
            len = rxBuf ? rxBuf[1] : 0u;
        } else {
            rf_diag.rx_crcerr++;
            ev = HAL_RF_EV_RX_CRCERR;
        }
        break;
    case TX_MODE_TX_FINISH:
        rf_diag.tx_done++;
        ev = HAL_RF_EV_TX_DONE;
        break;
    case TX_MODE_TX_FAIL:
        RF_DIAG_INC(tx_fail);           /* also written by hal_rf_start_tx: dual context */
        ev = HAL_RF_EV_TX_FAIL;
        break;
    default:
        /* Auto-mode states this basic-mode firmware never arms. The legacy
         * callback's switch default posted a defensive RX restart for them;
         * forward as RX_TIMEOUT (CH59x has no real RX-timeout state, so the
         * slot is free) and the sink replicates the legacy default. */
        rf_diag.rx_timeout++;
        rf_diag.rx_armed = 0u;          /* the timeout-shaped event ends the arm too */
        ev = HAL_RF_EV_RX_TIMEOUT;
        break;
    }
    if (rf_event_cb == 0) {
        return;
    }
    rf_event_cb(ev, rxBuf, len);
}

/* IAP 0x92 PHY diagnostics (page 1): the counters above. The radio-internal
 * fields the CH570 executor fills (channel, AA, timeout) stay 0 here. */
void hal_rf_diag_snapshot(hal_rf_diag_t *out)
{
    *out = rf_diag;
}

void hal_rf_diag2_snapshot(hal_rf_diag2_t *out)
{
    uint8_t *p = (uint8_t *)out;
    unsigned i;

    for (i = 0u; i < sizeof(*out); i++) {
        p[i] = 0u;
    }
}
