openkeyboard-org/OpenDongle/firmware/ch570/src/dongle_target.h

/*
 * OpenKeyboard.org OpenDongle
 * Copyright 2026 Eric Molitor (EMulator)
 * SPDX-License-Identifier: Apache-2.0
 */

#ifndef DONGLE_TARGET_H
#define DONGLE_TARGET_H

#include "version.h"

#define DONGLE_FW_VERSION FW_VERSION
#define DONGLE_CHIP_FAMILY_ID 0x70u

/* CODEREVIEW F01: the app carries the ODG2 identity header (family/kind/base/
 * magic at image offset 0x20; dongle_id.c stamps it). DONGLE_IAP_APP_BASE must
 * equal this chip's app ORIGIN(FLASH), which under OpenBoot's A/B slots is
 * the base of the slot THIS image was linked for, not a fixed address.
 * OpenBoot owns [0, 0x2000) and performs all flash updates in-bootloader
 * (linker-asserted in link.ld). */
#define DONGLE_IAP_IMAGE_ID 1
/* The app's load address IS its slot's base, so this must move with the slot:
 * dongle_id.c stamps it into the ODG2 header, and a slot-B image advertising
 * 0x2000 would be rejected by the host tooling that checks the two agree.
 * Taken from the same define openboot_app.c uses for its record address, so
 * there is one source of truth per build rather than two that can disagree. */
#ifdef OPENBOOT_SLOT_BASE
#define DONGLE_IAP_APP_BASE ((uint32_t)(OPENBOOT_SLOT_BASE))
#else
/* Only reachable where openboot_app.c is NOT compiled: it #errors without
 * OPENBOOT_SLOT_BASE and is in APP_SRC for both chips, so no firmware build
 * can reach this line. Host/standalone compiles of individual sources can. */
#define DONGLE_IAP_APP_BASE 0x2000u
#endif

/* PAIR_BCAST-to-pair-ACK turnaround. Two constraints bound it (bench-derived):
 *  - lower: the Bridge75 stock keyboard needs 1..8 ms between its broadcast
 *    and our LEN-15, and reconnects best at 2.5 ms (rf_task.c: 8/8, 0.11 s,
 *    0-1 flips vs 6/6, 0.22 s, up to 12 flips at 1.875 ms);
 *  - upper: the OpenController keyboard's bonded-reconnect search closes its
 *    receive window KBD_PAIR_RX_WINDOW_TICKS after it arms (power MR4). At
 *    4 ticks = 2.5 ms our ACK (software-measured: accept -> StartTx returned
 *    2538..2551 us, StartTx -> TX_FINISH callback ~214 us) completed on or
 *    about that closing edge -- consistent with, not sniffed -- and was missed
 *    EVERY time:
 *    a bonded dongle that had not connected since boot never reconnected
 *    (0 valid RX in 500 beacons, 3/3 cold boots, bench 2026-09-04), and only a
 *    fresh pair -- whose continuous-RX flavour tolerates the late ACK --
 *    recovered it. Resolved on the keyboard side (window widened to 6 ticks =
 *    3.75 ms) to keep this value at the Bridge75 optimum; 3u was bench-proven
 *    as the dongle-side alternative (6/6 cold, 5/5 after an EV10 give-up).
 *    Any keyboard window narrower than ~3 ms re-opens this collision. */
#define RF_CH570_PAIR_ACK_PRE_TX_TMOS 4u    /* 4 x 625 us = 2500 us */

/* P4 deaf-camp guard retry cadence. A terminal camp (give-up reacquire,
 * closed boot window) and the connected self-heal loop arm RF_Rx and then
 * lean on the radio's 30 ms camp timeout to re-drive RF_EVT_RX_RESTART; a
 * FAILED arm never starts the radio, so no timeout fires and the camp is
 * silently deaf forever. On a failed arm the guard schedules an independent
 * RF_EVT_RX_RESTART this many TMOS units out — comfortably above the 30 ms
 * camp window so retries don't stack, ~20/s to pace a persistent failure.
 * CAVEAT: hal_event_post_delayed() has only two delay slots; if both are
 * already held (both pair-prep PAIR_PREP and a pair-ACK burst in flight during
 * an active pairing attempt) the post DEGRADES to immediate and the retry
 * paces at the main-loop rate until a slot frees. That window is bounded (the
 * held deadlines mature in tens of ms) and self-limiting (the radio is already
 * broken and PAIR_PREP re-drives the scan there), so it thrashes rather than
 * hot-locks. The terminal camps that rely on the guard as their SOLE recovery
 * (give-up, closed boot window) first cancel PAIR_PREP and abort the burst, so
 * both slots are free there. See rf_arm_retry_if_failed() in rf_task.c. */
#define RF_ARM_RETRY_TMOS 80u               /* 80 x 625 us = 50 ms */
#define CH570_RF_START_AFTER_USB_CONFIG_DELAY_MS 1000u

/* CH570 remote wake: advertise DEVICE_REMOTE_WAKEUP and let the shared USB
 * driver arm/drive wake via the CH570 main-loop service call. */
#define DONGLE_USB_REMOTE_WAKEUP 1

/* Tsys timing constants for the shared rf_task (P4). The CH570 Tsys clock is
 * CH570_SYSCLK_HZ (fixed 100 MHz — the only supported CH570 clock) —
 * both divide the microsecond and the 1/32000 s protocol tick exactly. */
#define HAL_TICKS_PER_US        (CH570_SYSCLK_HZ / 1000000u)
#define HAL_TMOS_UNIT_TICKS     (625u * HAL_TICKS_PER_US)
#define HAL_TICKS_PER_PROTO_TICK (HAL_TICKS_PER_US * 125u / 4u)
_Static_assert(HAL_TICKS_PER_PROTO_TICK * 32000u
               == HAL_TICKS_PER_US * 1000000u,
               "protocol tick must divide the Tsys clock exactly");
_Static_assert((CH570_SYSCLK_HZ % 1000000u) == 0u,
               "CH570 Tsys clock must be a whole MHz");

/* RF-task executor model: the CH570 has no TMOS — the shared rf_task is
 * driven by the polled pump (hal_dispatch_ch570 + RF_TaskPump). */
#define RF_TASK_EXECUTOR_TMOS 0

/* Gate the durable bond write on a confirmed connected RX from the peer, so a
 * fresh pair that promoted on our own pair-ACK TX-finish alone (no keyboard
 * confirm) never persists a dead bond. Decoupled from the executor macro on
 * purpose (Issue #23): the confirm-before-persist state machine is shared, only
 * the durable-arm site and the CX4 write differ per executor. */
#define RF_CONFIRM_BEFORE_PERSIST 1

#define DONGLE_HAS_RF 1

/* The bond sits at 0x3A000, immediately above the OBP-clamped app region
 * (the OpenBoot board file sets OB_APP_END there), so no ERASE/WRITE/COMMIT
 * can reach it.
 *
 * It is NOT displaced by an OpenBoot record any more: under A/B slots each
 * slot's record lives in the top erase block of its own slot (0x1D000 for
 * slot A, 0x39000 for slot B), and 0x3B000 — which used to hold the record —
 * is now an unused spare page that our clamp keeps out of reach as well. */
#define CH570_BOND_FLASH_ADDR 0x3A000u
#define CH570_BOND_FLASH_SIZE 0x1000u

/* What erased flash reads as through the XIP/FLASH_ROM descrambler (the
 * fixed per-4-byte XOR key 56 42 06 0C over physical 0xFF cells). Used by
 * dongle_nv_is_erased() to controller-VERIFY the bond page really erased
 * (F26: the XIP view can serve stale bytes after a controller write). */
#define CH570_FLASH_ERASED_WORD 0xF3F9BDA9u

#endif /* DONGLE_TARGET_H */
