openkeyboard-org/OpenDongle/firmware/validation/read_aes_log.py

#!/usr/bin/env python3
"""Decode the AES validation log the on-device harness leaves in RAM.

Copyright 2026 Eric Molitor (EMulator)
SPDX-License-Identifier: Apache-2.0

Every result from this campaign so far was decoded BY HAND out of a hex dump.
That is slow, and worse, it is the step where a tired reader confirms the number
they expected to see. This module is the machine-checked replacement.

Two design rules, both learned the hard way:

  - MARKER CONSTANTS ARE PARSED FROM `aes_log_format.h`, never redeclared here.
    A reader carrying its own copy of the wire format is a reader that will one
    day disagree with the firmware and be believed anyway.

  - THE DEVICE'S OWN PASS FLAG IS NOT TRUSTED. The harness compares ciphertext
    on-device and logs a boolean, but it also logs the ciphertext itself, and
    `verify()` re-checks the bytes against expectations supplied by the caller.
    A backend whose comparison is broken reports success in that boolean; only
    an independent check catches it. This is what the plan means by comparing
    byte-for-byte rather than by checksum.

A desync is reported, never worked around. If an unexpected word turns up where
a marker belongs, parsing stops with the offset -- resynchronising by scanning
forward would eventually land on payload data that happens to look like a
marker and produce a confident, wrong report.
"""

from __future__ import annotations

import argparse
import re
import struct
import sys
from dataclasses import dataclass, field
from pathlib import Path

HEADER = Path(__file__).resolve().parent / "aes_log_format.h"
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
